alexandrasalazarz-lgtm/FunBioG14./ENTREGABLES/Taller 8/tati-quispe-cueva-bf5b25a1-1941-4490-aaff-6f8eaddafe3f-certificate.pdf

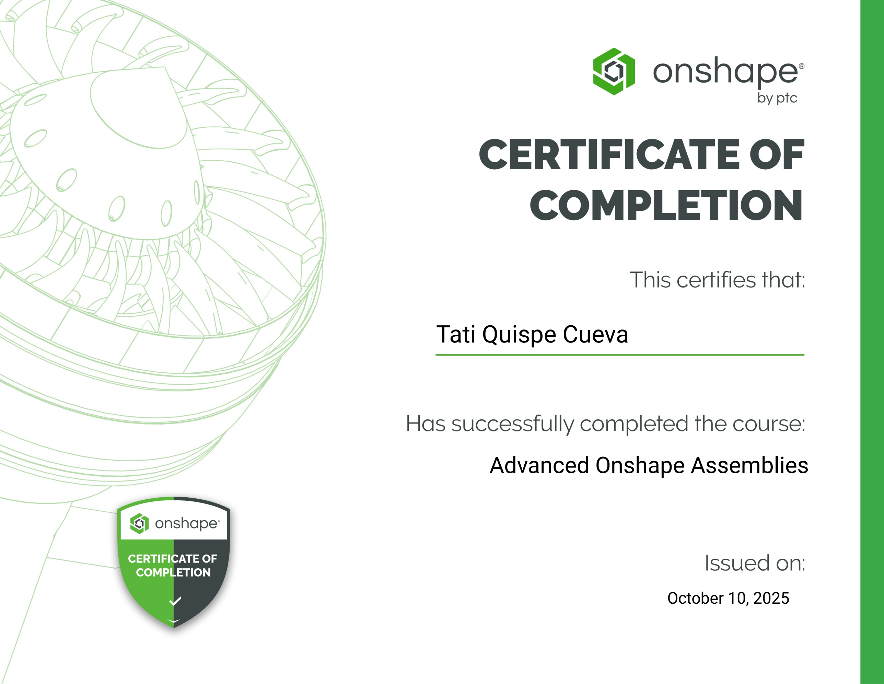
[picture p25: page 1]

Tati Quispe Cueva

Advanced Onshape Assemblies

October 10, 2025
