alexandrasalazarz-lgtm/FunBioG14./ENTREGABLES/Taller 8/sebastian-reymundo-b19e6a7e-2497-46d5-aa7a-b30fd2726343-certificate.pdf

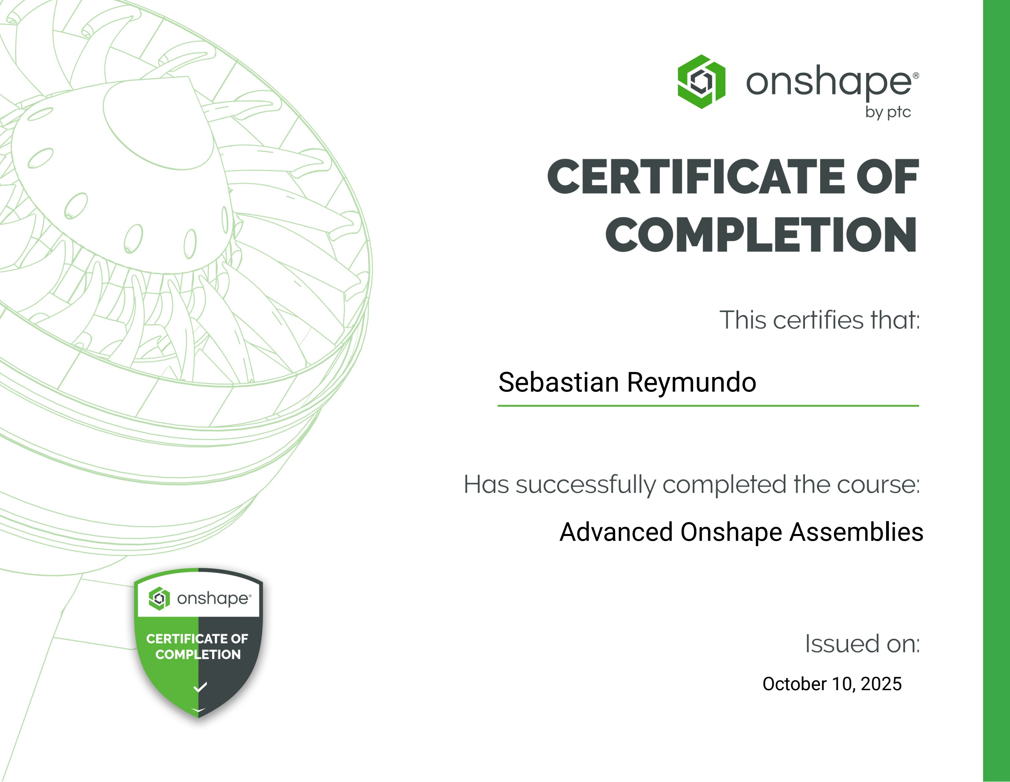
[picture p26: page 1]

Sebastian Reymundo

Advanced Onshape Assemblies

October 10, 2025
