alexandrasalazarz-lgtm/FunBioG14./ENTREGABLES/Taller 8/Luciana-Saenz-e1a2f70c-e385-4446-b01d-66b528b82a3a-certificate.PDF

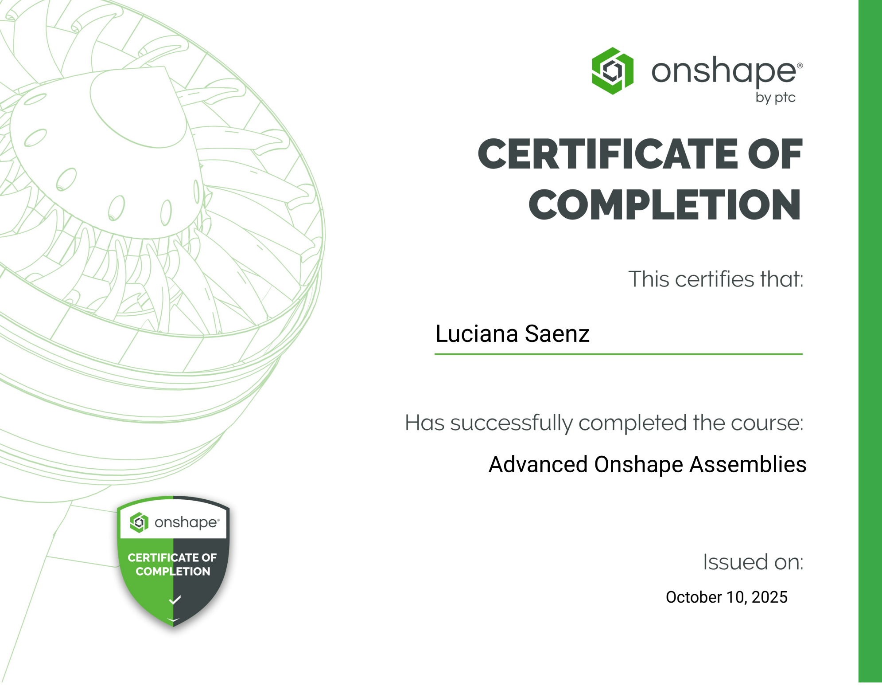
[picture p27: page 1]

Luciana Saenz

Advanced Onshape Assemblies

October 10, 2025
