alexandrasalazarz-lgtm/FunBioG14./ENTREGABLES/Taller 8/alexandra-salazar-3b08da2b-9840-4f47-ac77-2912e088a5ac-certificate.pdf

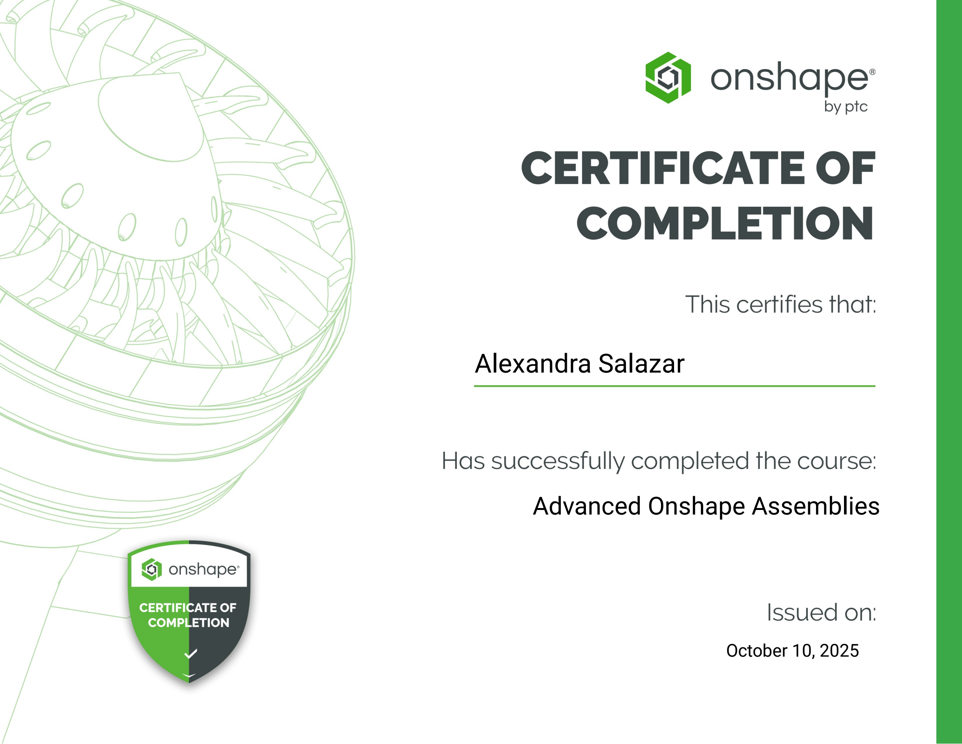
[picture p28: page 1]

Alexandra Salazar

Advanced Onshape Assemblies

October 10, 2025
