alexandrasalazarz-lgtm/FunBioG14./ENTREGABLES/Entregable 5/Sebastian Reymundo/Onshape Fundamentals CAD.pdf

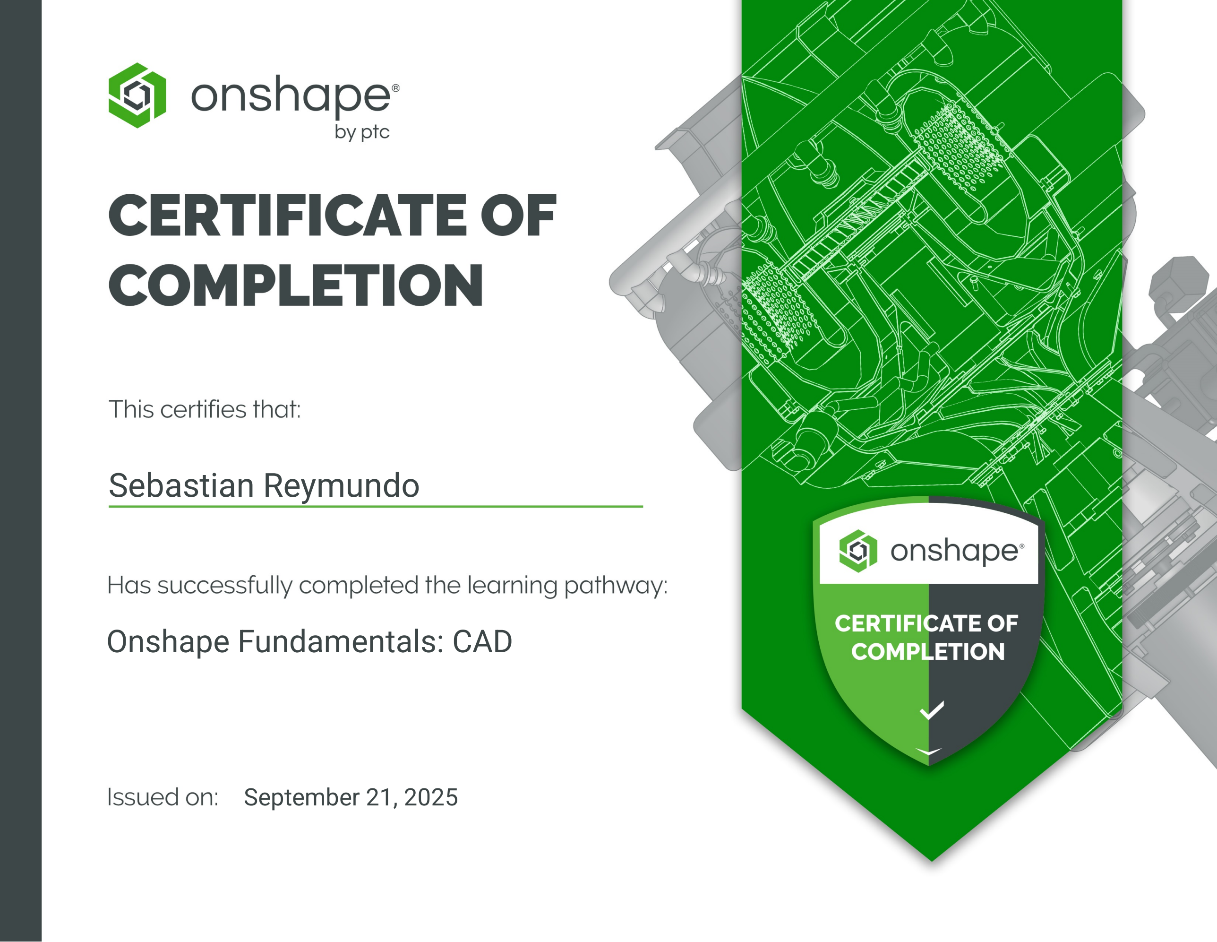
[picture p29: page 1]

Onshape Fundamentals: CAD

September 21, 2025

Sebastian Reymundo
