alexandrasalazarz-lgtm/FunBioG14./ENTREGABLES/Entregable 5/Luciana Saenz/luciana-saenz-2468588a-6642-499a-9439-9e74ae3b6bcc-certificate.pdf

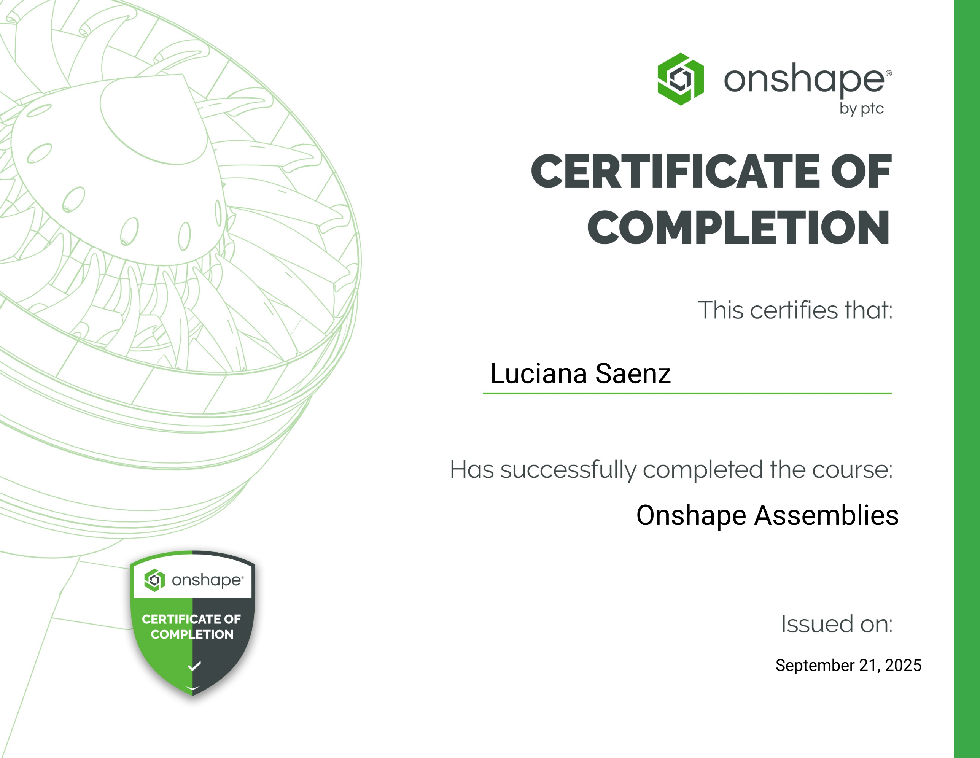
[picture p30: page 1]

Luciana Saenz

September 21, 2025

Onshape Assemblies
