alexandrasalazarz-lgtm/FunBioG14./ENTREGABLES/Entregable 5/Tatiana Quispe/tati-quispe-cueva-7f686d76-14ea-4a70-ba4c-fde4c63a0db2-certificate.pdf

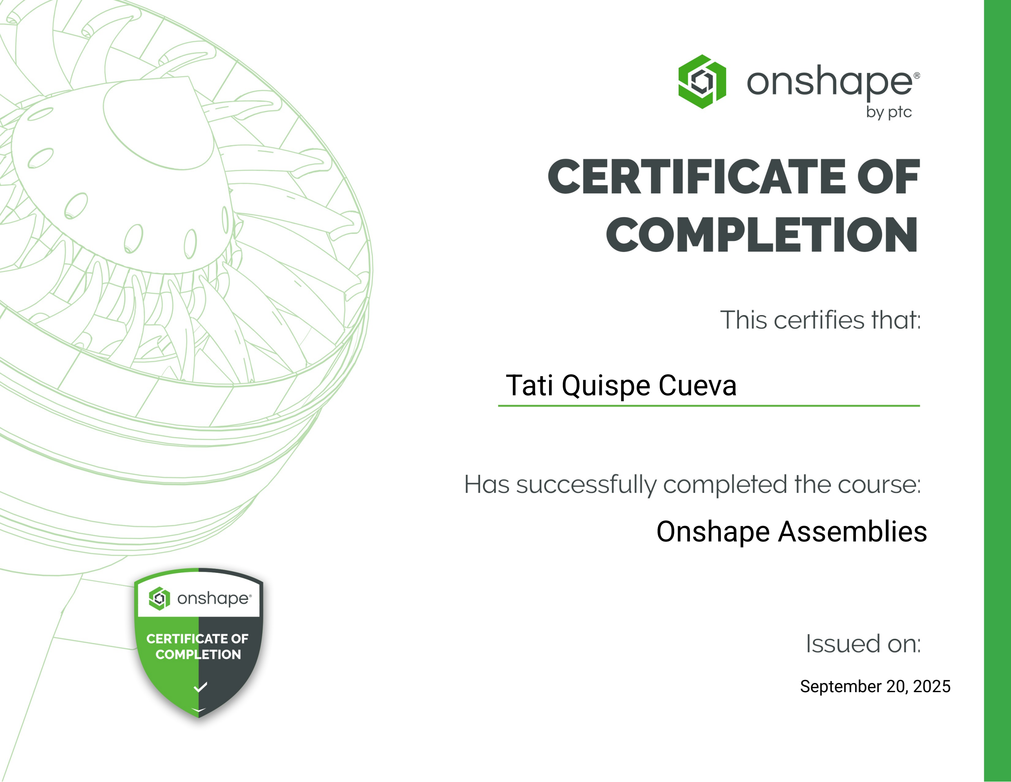
[picture p31: page 1]

Tati Quispe Cueva

September 20, 2025

Onshape Assemblies
