alexandrasalazarz-lgtm/FunBioG14./ENTREGABLES/Entregable 5/Alexandra Salazar/alexandra-salazar-a3af0b42-a987-454b-bc5e-5e8b458e8664-certificate.pdf

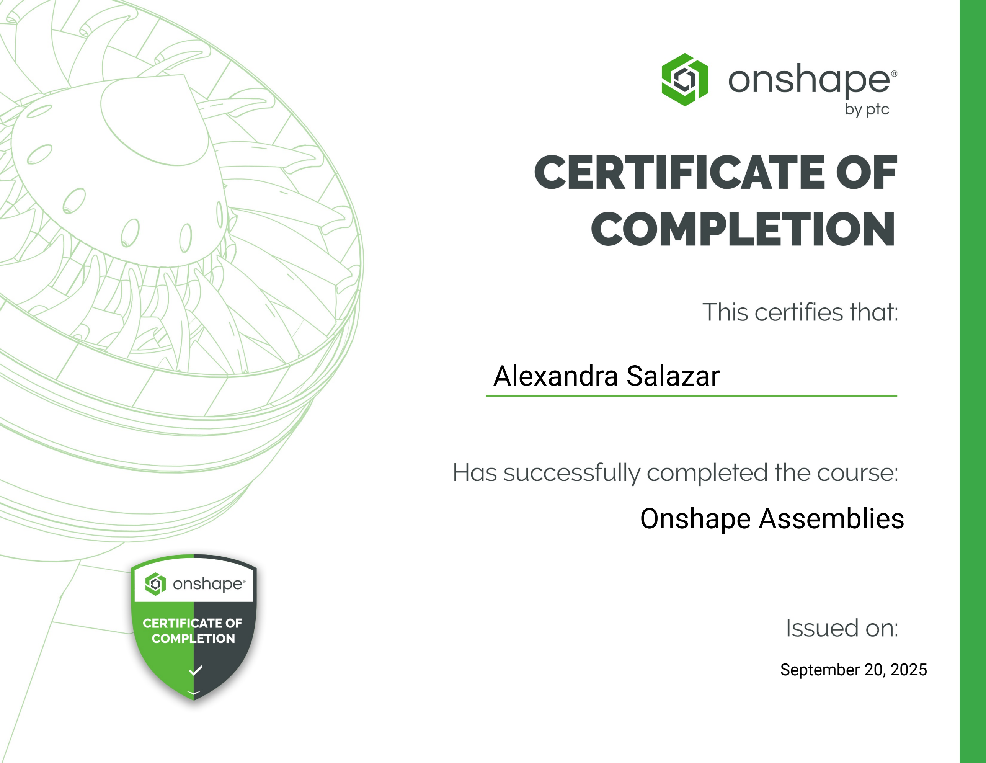
[picture p32: page 1]

Alexandra Salazar

September 20, 2025

Onshape Assemblies
