alexandrasalazarz-lgtm/FunBioG14./ENTREGABLES/Entregable 5/Alexandra Salazar/alexandra-salazar-1867dc95-b322-4a8a-b071-154235bd6980-certificate (1).pdf

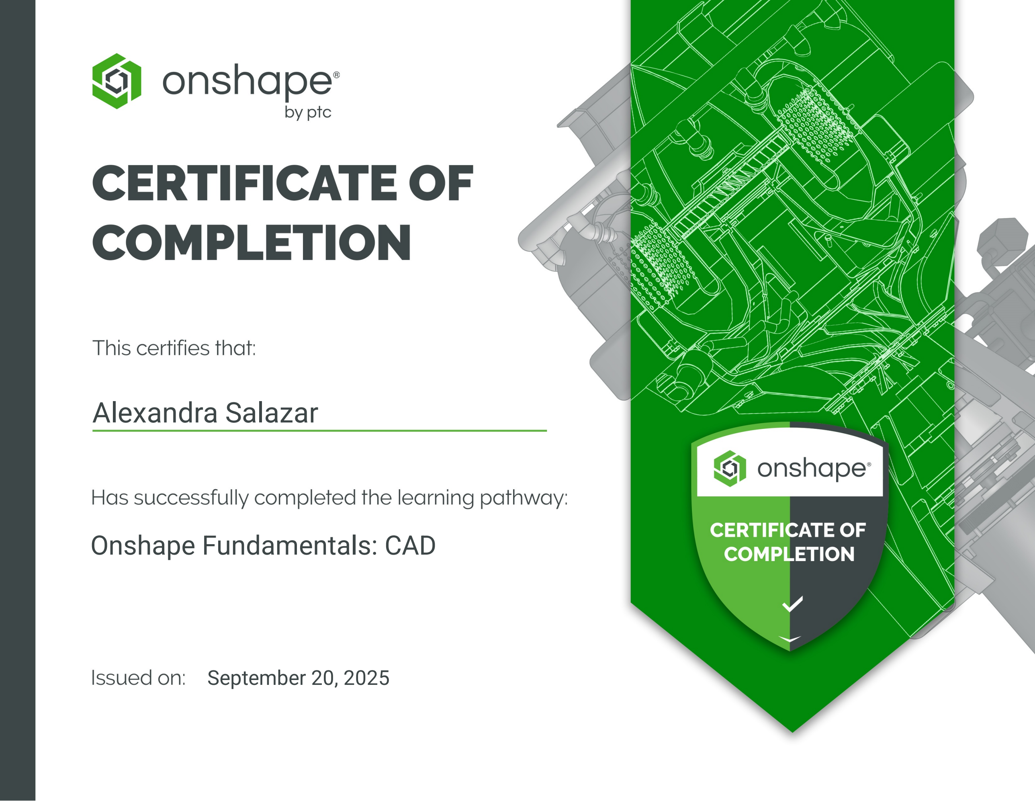
[picture p33: page 1]

Onshape Fundamentals: CAD

September 20, 2025

Alexandra Salazar
