alexandrasalazarz-lgtm/FunBioG14./DOCUMENTOS/HITO 2/HITO 2 presentación.pdf

## Fundamentos de Biodiseño

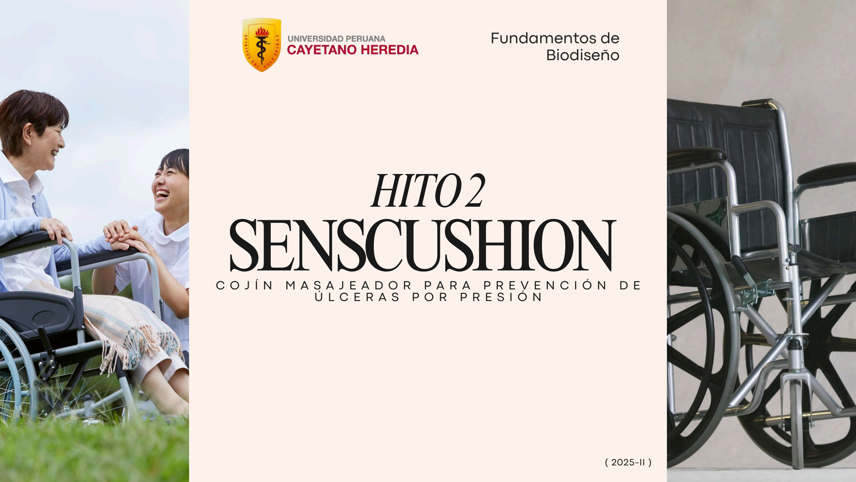
[picture p95: page 1]

# SENSCUSHION

( 2025-II )

# HITO2

C O J Í N | M A S A J E A D O R | P A R A | P R E V E N C I Ó N | D E
Ú L C E R A S | P O R | P R E S I Ó N

# INTEGRANTES: Rodríguez Cruz, Ivanna Jael (Investigación, Diseñadora y Programadora

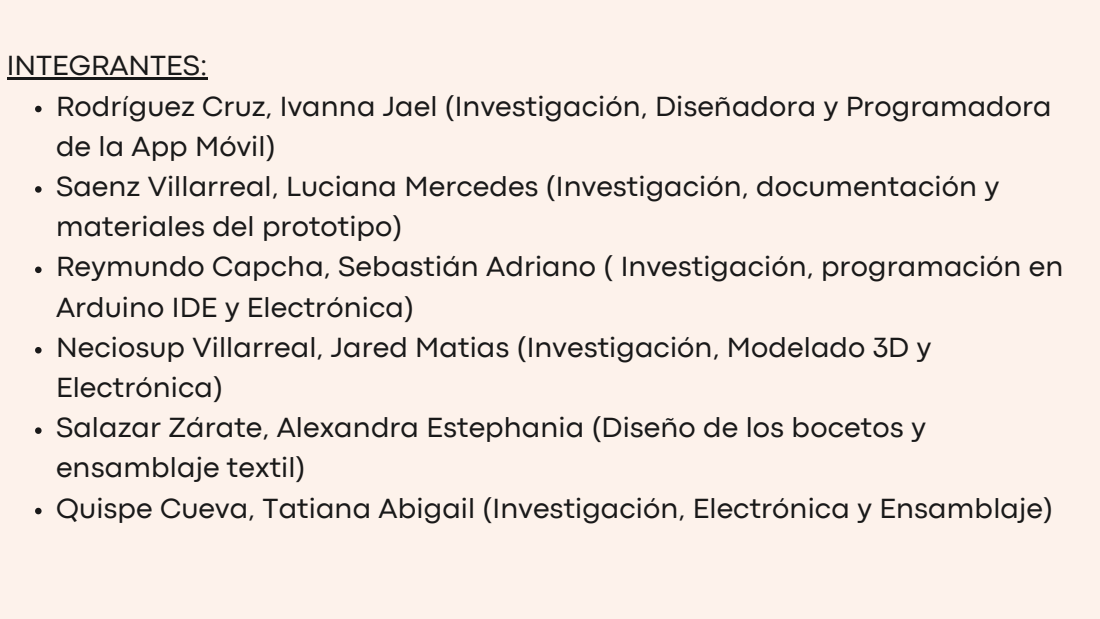
[picture p96: page 2]

de la App Móvil)
Saenz Villarreal, Luciana Mercedes (Investigación, documentación y
materiales del prototipo)
Reymundo Capcha, Sebastián Adriano ( Investigación, programación en
Arduino IDE y Electrónica)
Neciosup Villarreal, Jared Matias (Investigación, Modelado 3D y
Electrónica)
Salazar Zárate, Alexandra Estephania (Diseño de los bocetos y
ensamblaje textil)
Quispe Cueva, Tatiana Abigail (Investigación, Electrónica y Ensamblaje)

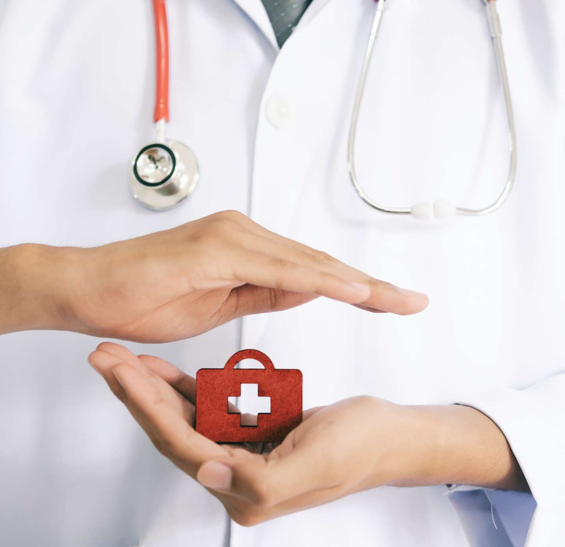
[picture p97: figure]

Í
N

D

I

C

E

( 0 7 )

0

1

## HIT

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
DIGIT
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
LIMIT

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
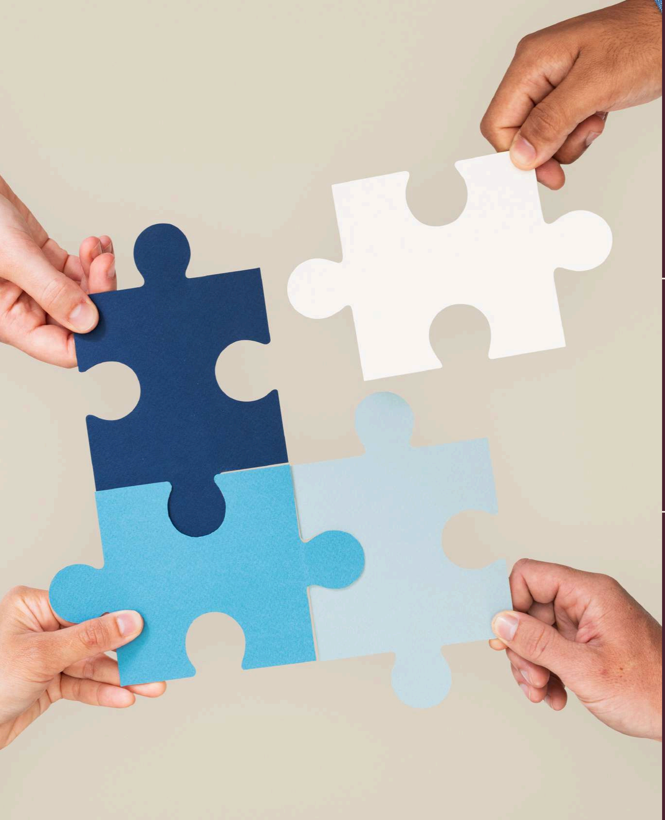
[picture p98: figure]

# PROBLEMÁTICA

## HITO 2

## FUNDAMENTOS DE BIODISEÑO

01

# Úlcerasporpresión

Se desarrolla cuando se bloquea el suministro de sangre a un área del cuerpo porque hay una presión excesiva y prolongada sobre la misma. En consecuencia, la piel en esa área comienza a morir, lo que resulta en una área abierta como un cráter o úlcera en la piel. [1]

FUNDAMENTOS DE BIODISEÑO | HITO 2 | ( 2025-II )

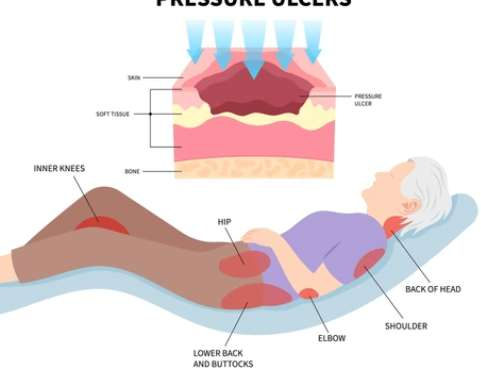
[picture p99: figure]

# Estadísticas

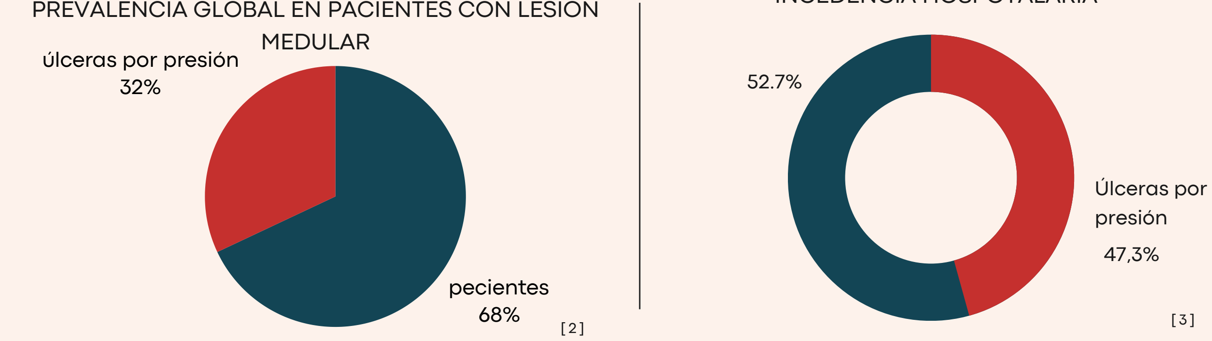
[picture p100: figure]
pecientes 68%; úlceras por presión 32%; Úlceras por; presión; MEDULAR

## PREVALENCIA GLOBAL EN PACIENTES CON LESIÓN

## INCEDENCIA HOSPOTALARIA

# Factoresderiesgo

FUNDAMENTOS DE BIODISEÑO | HITO 2 | ( 2025-II )

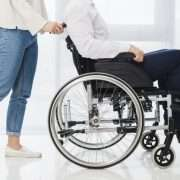
[picture p101: figure]

INMOVILIDAD
PROLONGADA

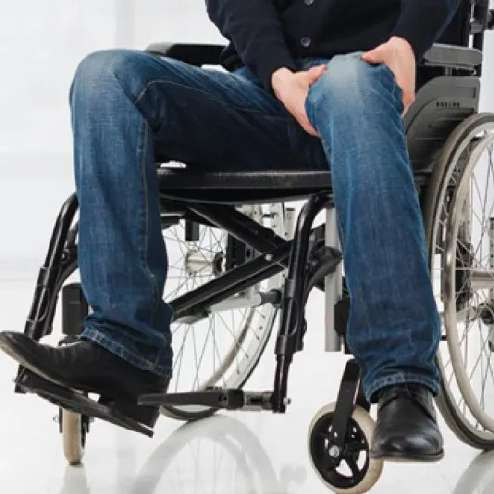
[picture p102: figure]

PÉRDIDA DE
SENSIBILIDAD

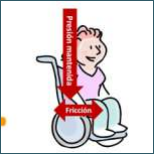
[picture p103: figure]
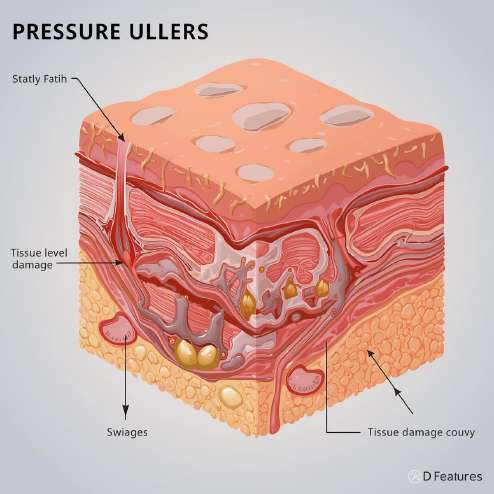
[picture p104: figure]
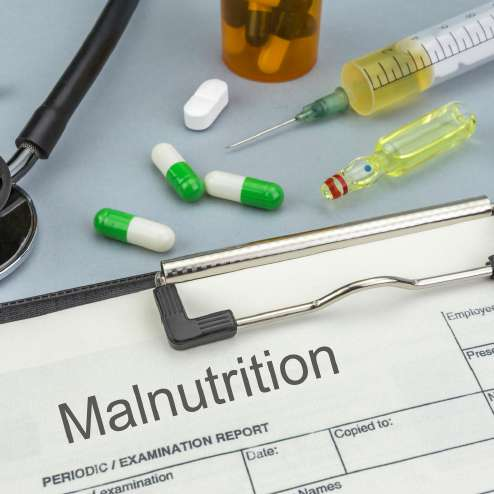
[picture p105: figure]

FRICCIÓN | HUMEDAD | MALNUTRICIÓN

# Cargaeconómica:

## Tratamiento de úlceras por presión genera

## costes directos significativos para el paciente [5]

[4]

# NECESIDADIDENTIFICADA

FUNDAMENTOS DE BIODISEÑO | ( PORTFOLIO DE TRABAJOS ) | 2025-II

# “Faltade un sistemaefectivoy accesibleparalaprevención de úlcerasporpresión

”

# Estadodelarte

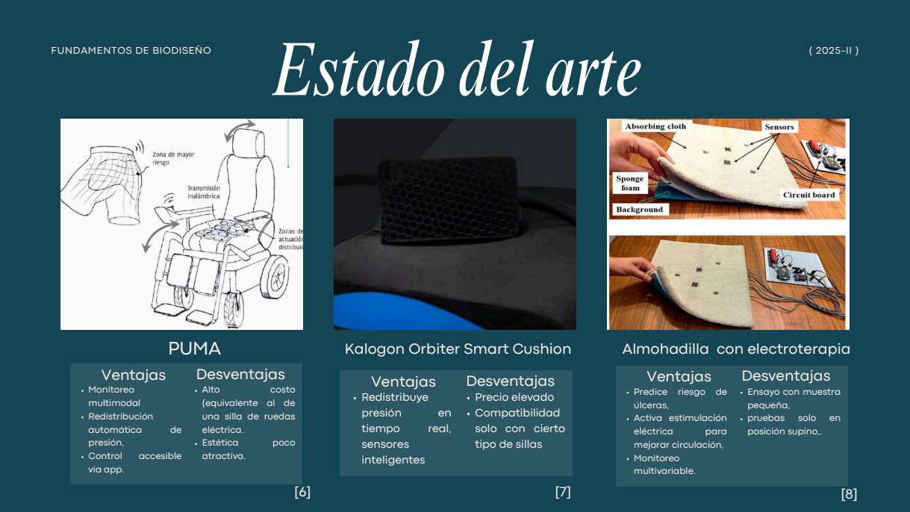
[picture p106: page 8]
PUMA; FUNDAMENTOS DE BIODISEÑO; Kalogon Orbiter Smart Cushion; Almohadilla con electroterapia; Ventajas; Desventajas; Monitoreo; multimodal; Redistribución; automática; presión,; Control; accesible; vía app.; Alto; costo; Estética; poco; Redistribuye; presión; tiempo; real,; sensores; inteligentes; Predice; riesgo; úlceras,; Activa estimulación; eléctrica; para; mejorar circulación,; multivariable.; pruebas; solo

(equivalente al de
una silla de ruedas
eléctrica.
atractiva.

Ensayo con muestra
pequeña,
posición supino,.

Precio elevado
Compatibilidad
solo con cierto
tipo de sillas

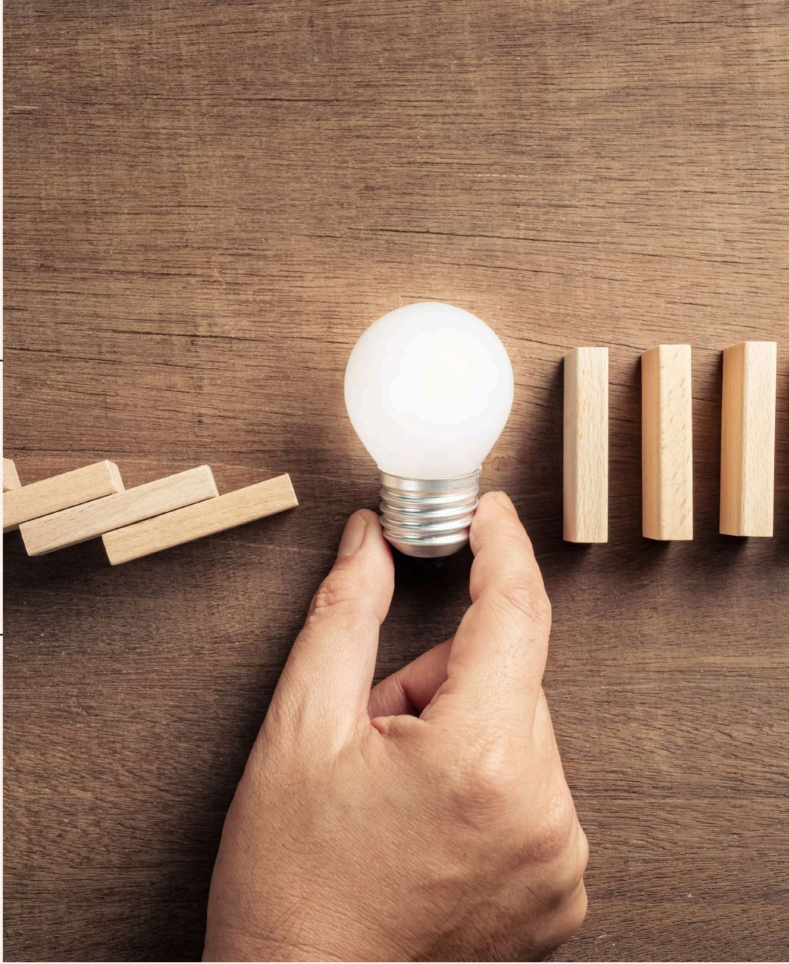
[picture p107: figure]

# SOLUCIÓN

## HITO 2

## FUNDAMENTOS DE BIODISEÑO

02

# SOLUCIÓN

FUNDAMENTOS DE BIODISEÑO | HITO 2

# “Cojín preventivo de úlceras por presión con

# masaje vibracionales”

# FUNCIONAMIENTO

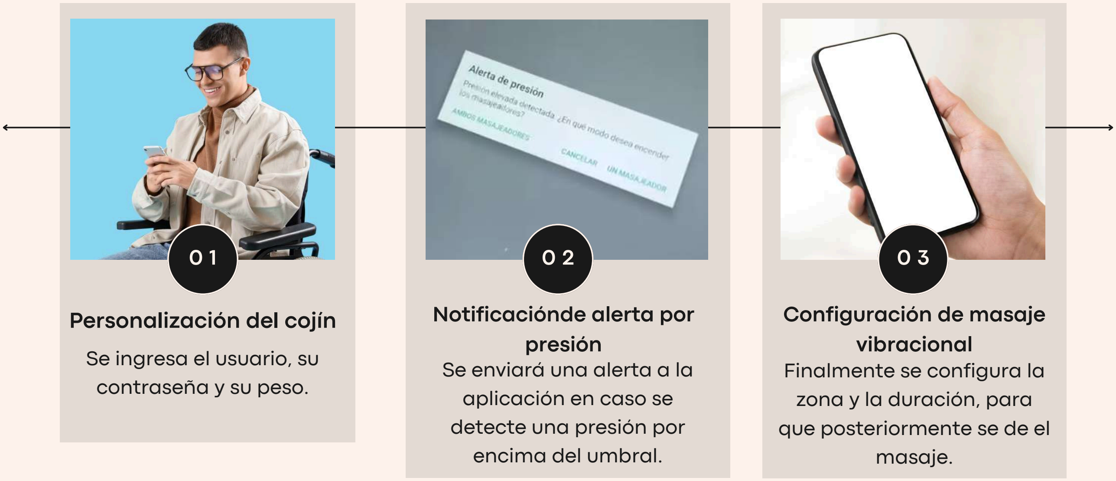
[picture p108: figure]
Se ingresa el usuario, su; contraseña y su peso.; Personalización del cojín; Se enviará una alerta a la; aplicación en caso se; detecte una presión por; encima del umbral.; Notificaciónde alerta por; presión; Finalmente se configura la; zona y la duración, para; que posteriormente se de el; masaje.; Configuración de masaje; vibracional

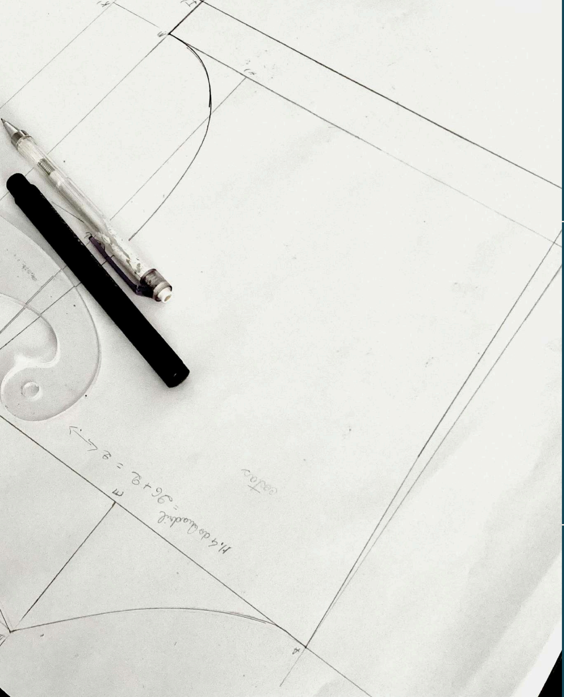
[picture p109: figure]

# BOCETO Y MODELADO

## HITO 2

## FUNDAMENTOS DE BIODISEÑO

03

# Bocetoymodelado

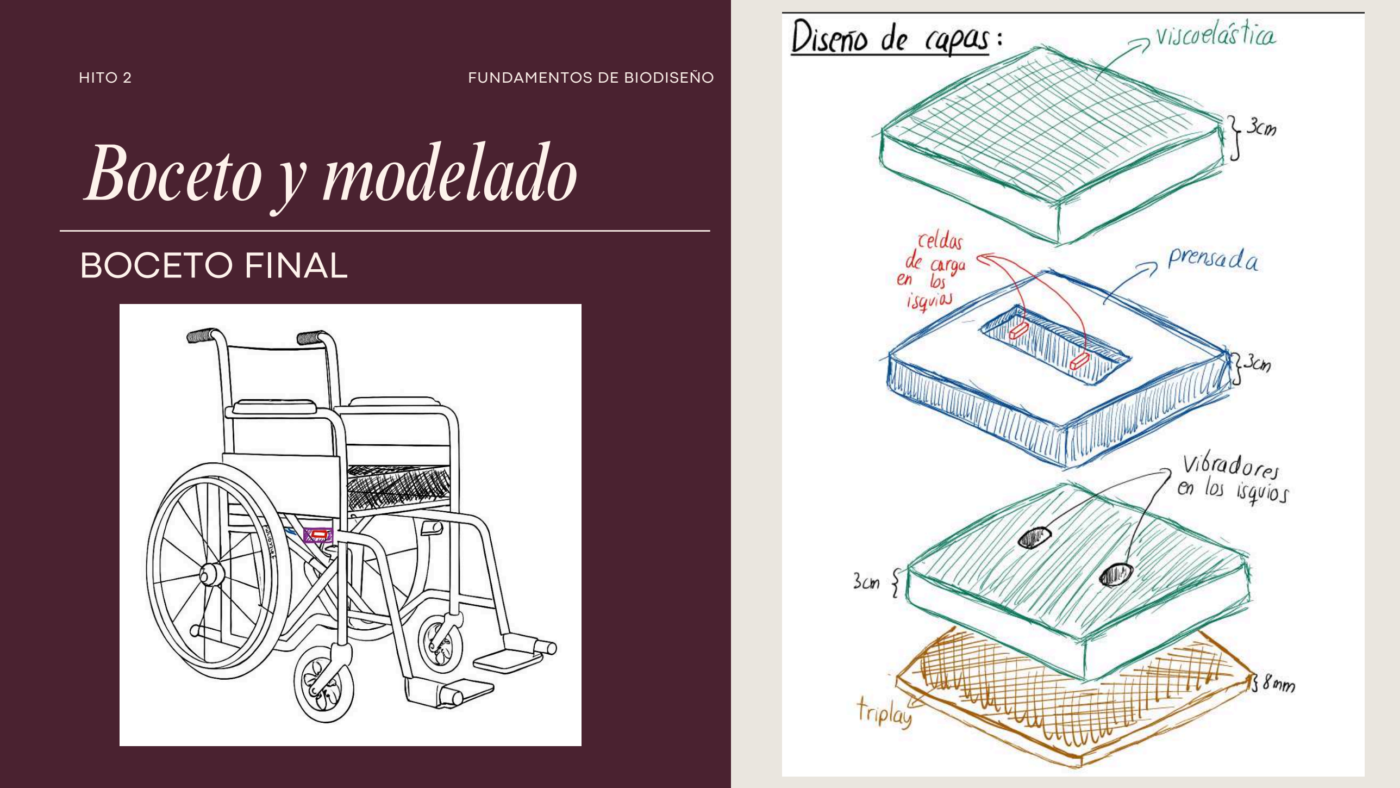
[picture p110: page 12]

HITO 2 | FUNDAMENTOS DE BIODISEÑO

# BOCETO FINAL

HITO 2 | FUNDAMENTOS DE BIODISEÑO | HITO 2

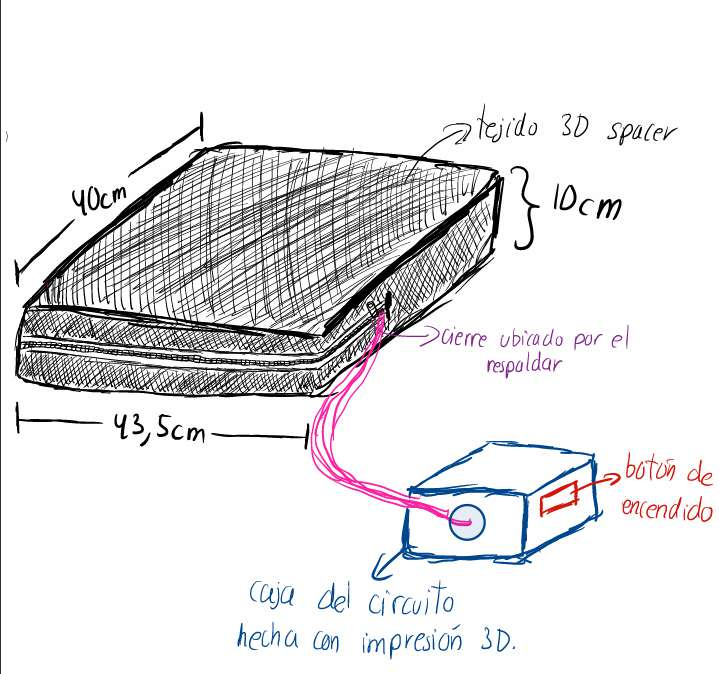
[picture p111: figure]

# MODELADO3D

HITO 2 | FUNDAMENTOS DE BIODISEÑO | HITO 2

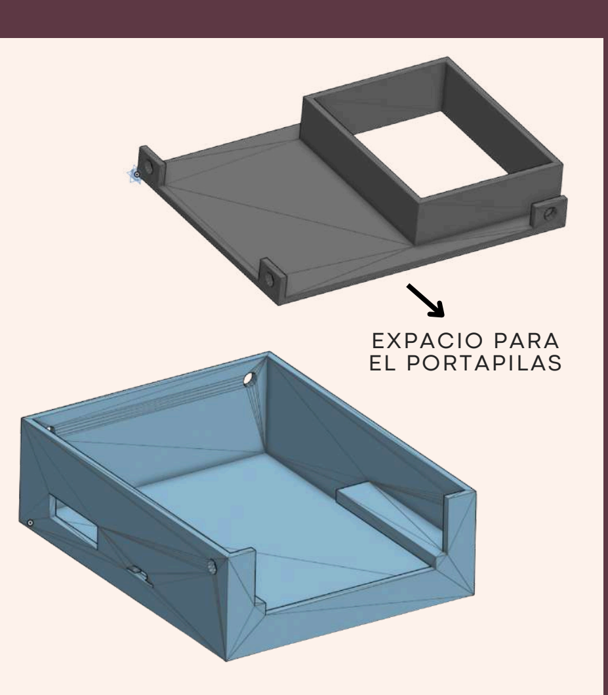
[picture p112: figure]
EXPACIO PARA EL PORTAPILAS
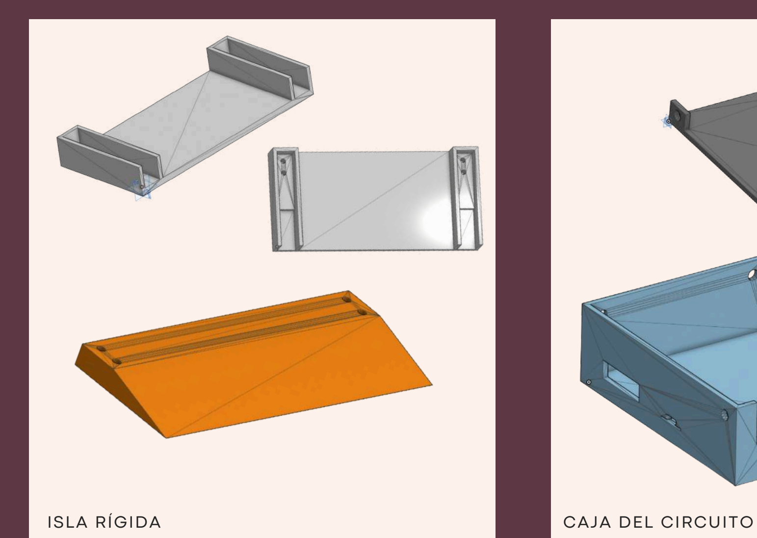
[picture p113: figure]
ISLA RÍGIDA; CAJA DEL CIRCUITO

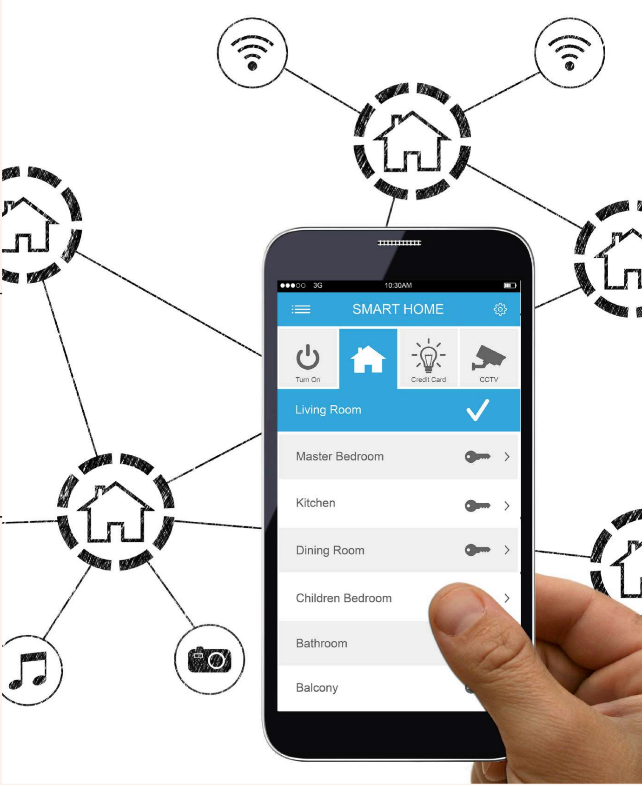
[picture p114: figure]

# APLICATIVO

## HITO 2

## FUNDAMENTOS DE BIODISEÑO

04

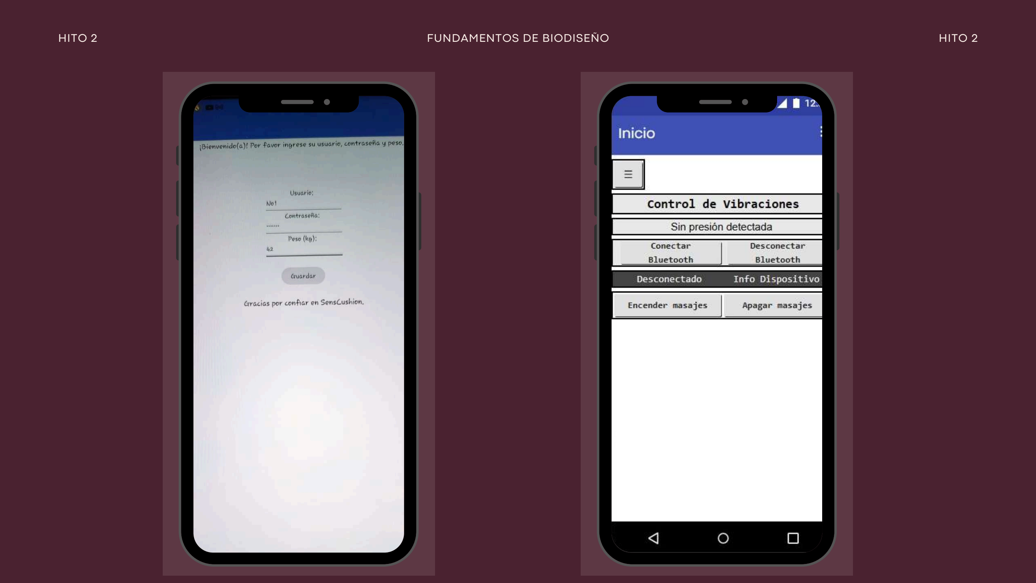
[picture p115: page 16]

HITO 2 | FUNDAMENTOS DE BIODISEÑO | HITO 2

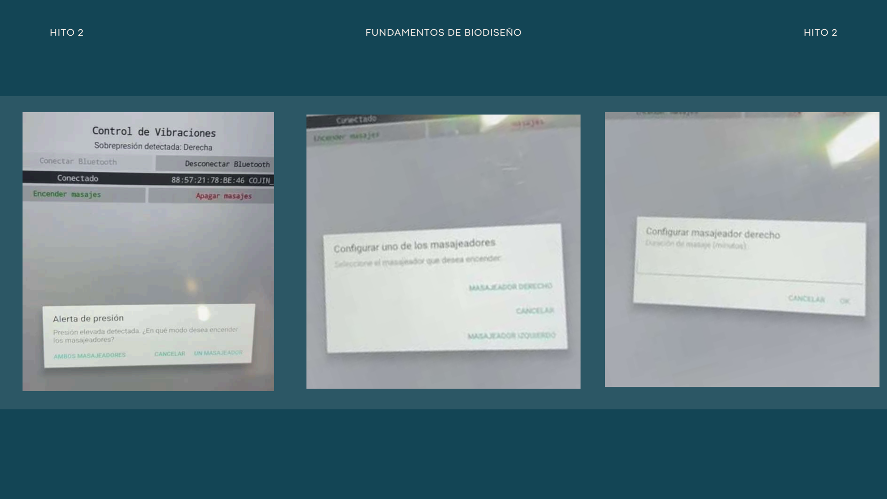
[picture p116: page 17]

HITO 2 | FUNDAMENTOS DE BIODISEÑO | HITO 2

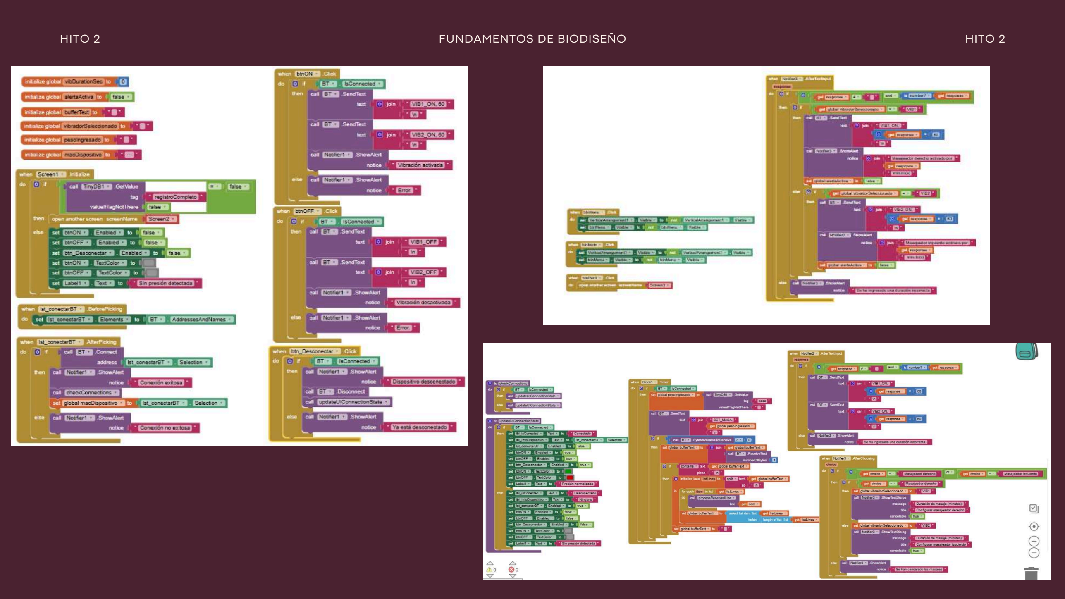
[picture p117: page 18]

HITO 2 | FUNDAMENTOS DE BIODISEÑO | HITO 2

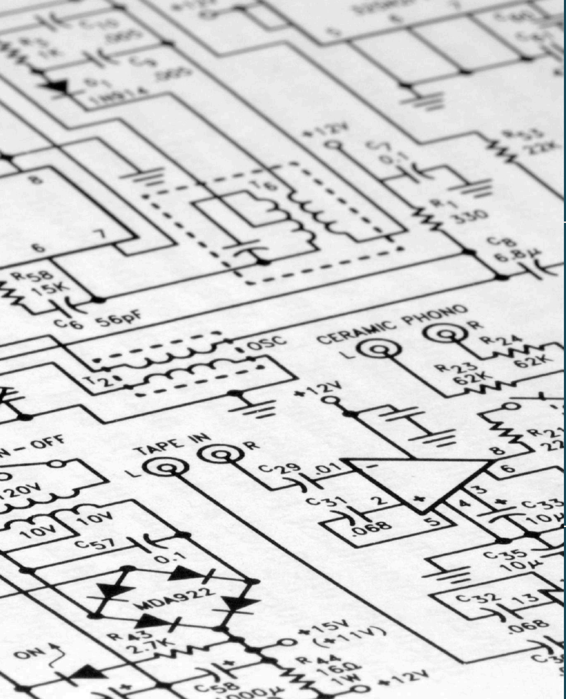
[picture p118: figure]

# DIAGRAMADEL PROTOTIPO

## HITO 2

## FUNDAMENTOS DE BIODISEÑO

05

# Diagramaesquemáticodelprototipoelectrónico

FUNDAMENTOS DE BIODISEÑO | HITO 2 | ( 2025-II )

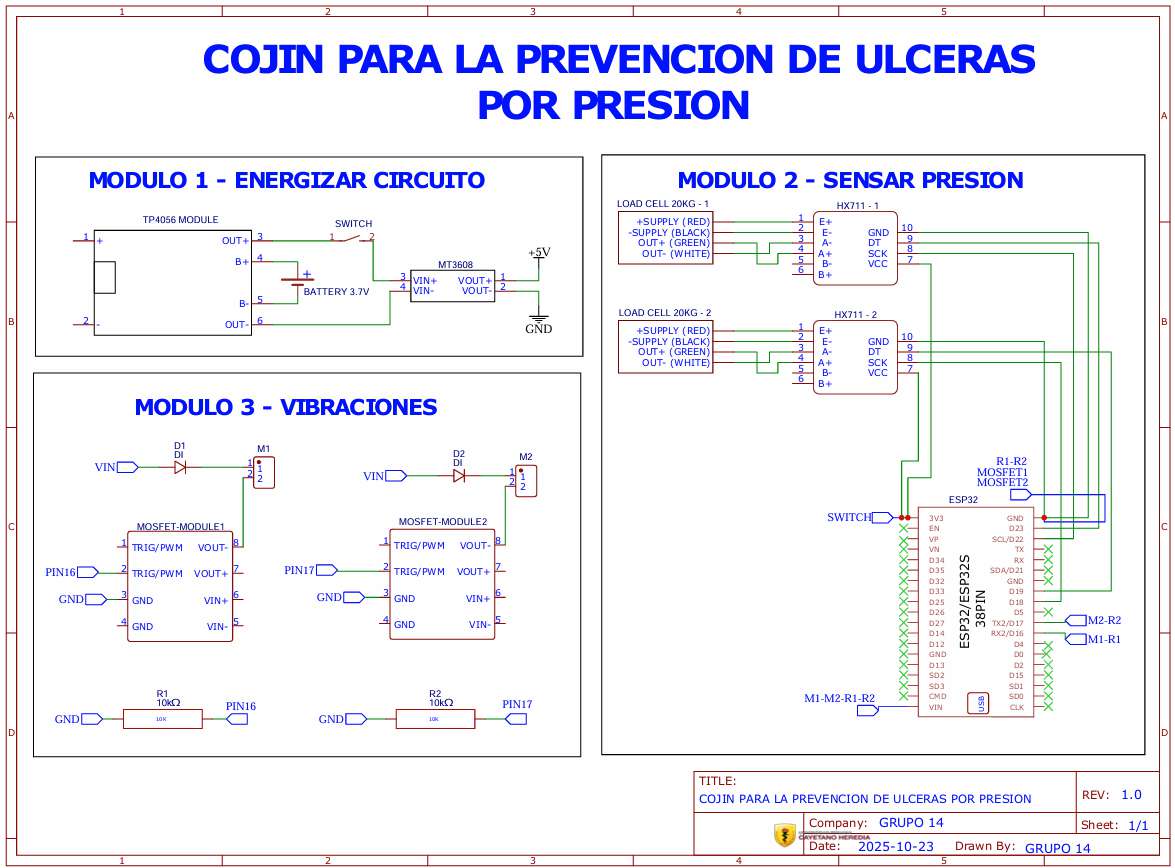
[picture p119: figure]

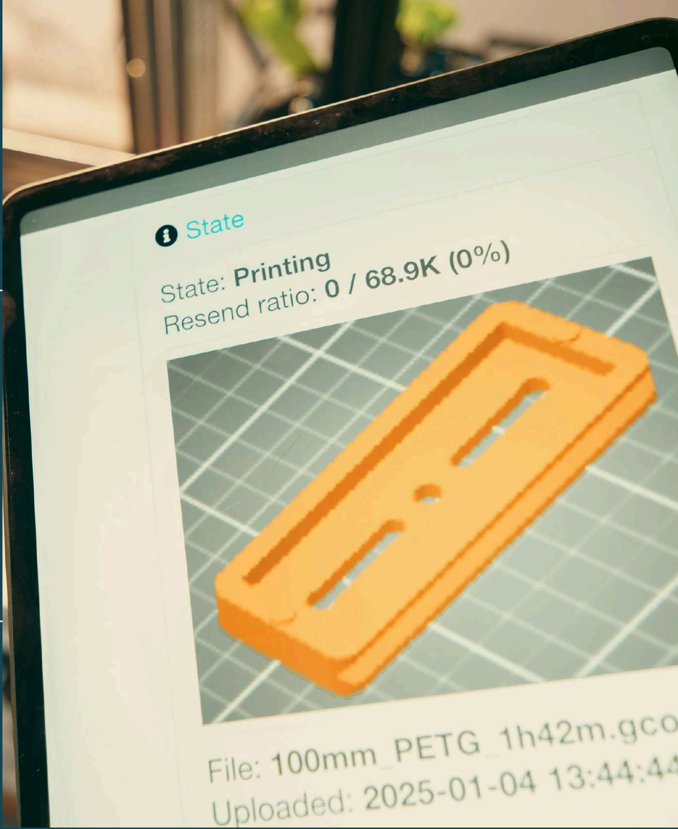
[picture p120: figure]

# MANUFACTURA DIGITAL

## HITO 2

## FUNDAMENTOS DE BIODISEÑO

06

# PROCESO DE ENSAMBLAJE

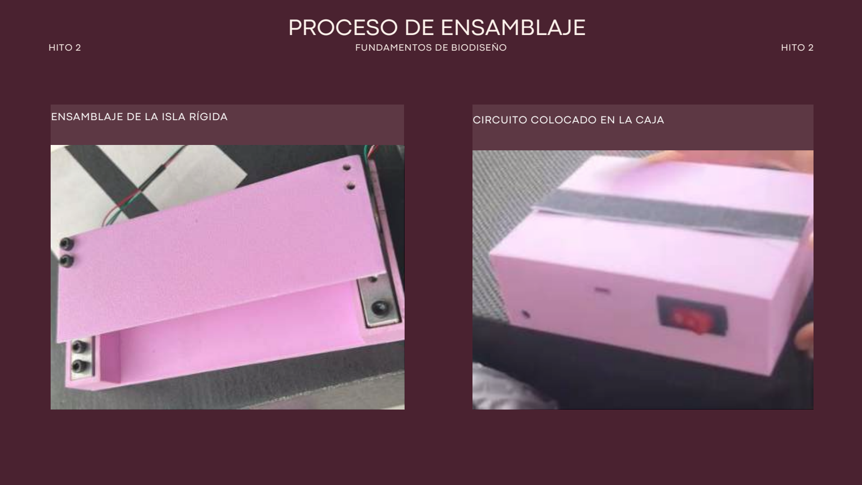
[picture p121: page 22]

ENSAMBLAJE DE LA ISLA RÍGIDA | CIRCUITO COLOCADO EN LA CAJA
HITO 2 | FUNDAMENTOS DE BIODISEÑO | HITO 2

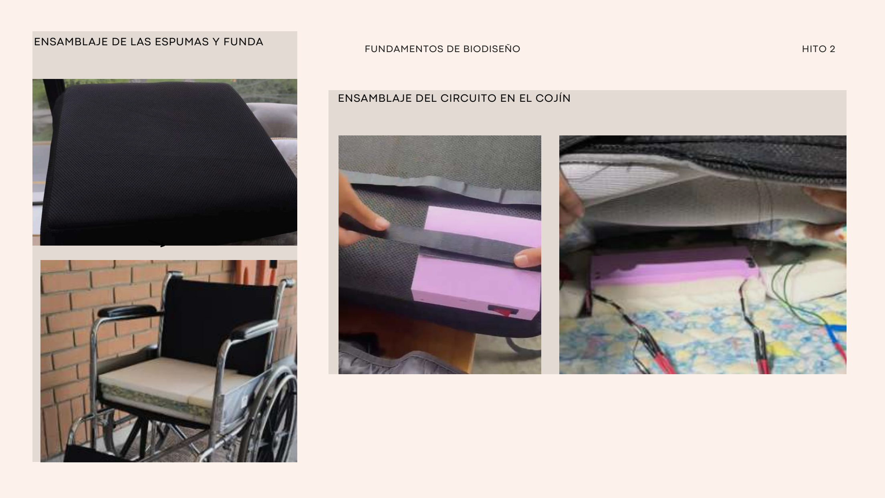
[picture p122: page 23]

ENSAMBLAJE DE LAS ESPUMAS Y FUNDA

ENSAMBLAJE DEL CIRCUITO EN EL COJÍN

FUNDAMENTOS DE BIODISEÑO | HITO 2

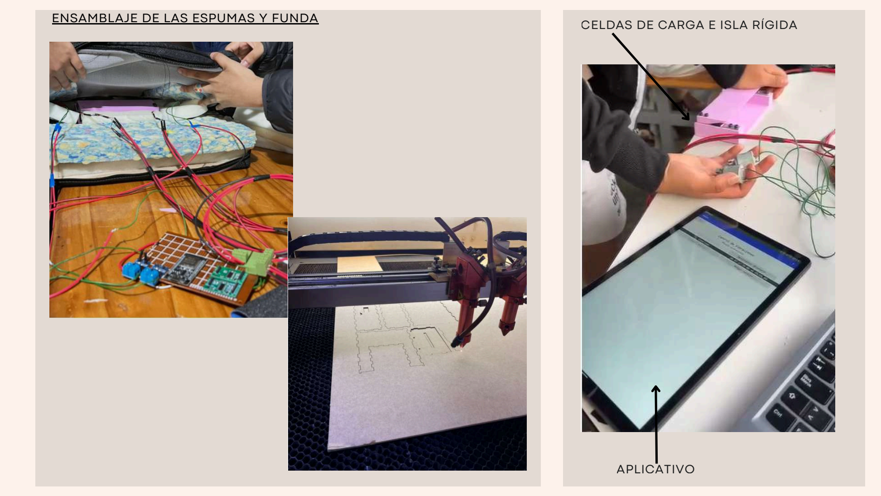
[picture p123: page 24]

CELDAS DE CARGA E ISLA RÍGIDA

APLICATIVO

ENSAMBLAJE DE LAS ESPUMAS Y FUNDA

Ga

# lle

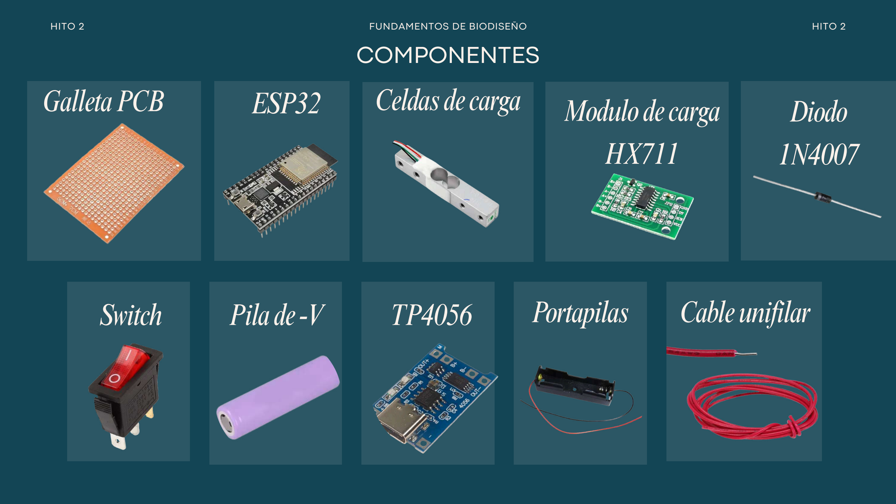
[picture p124: page 25]

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
# ifi

la
r

ta

P

CB

# ESP3

2

Ce

# lda

s

de
ca

# rga

Sw

# itch

Po

# rtap

i

la

# s COM

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
# rga

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
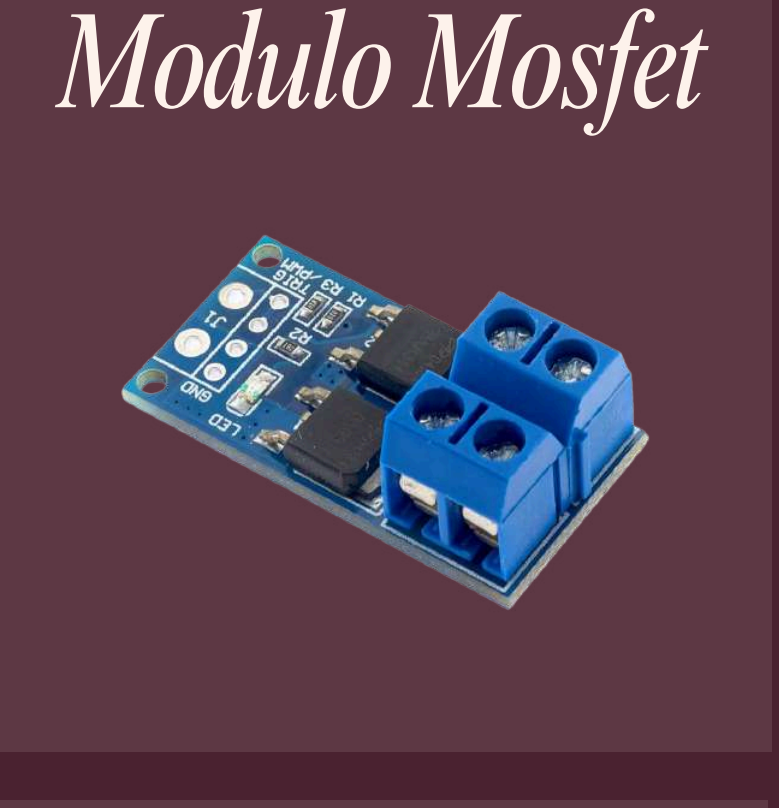
[picture p125: figure]
ModuloMosfet
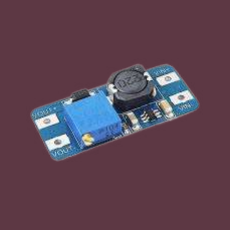
[picture p126: figure]
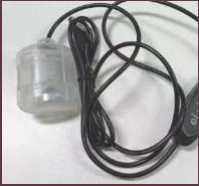
[picture p127: figure]

# Resistencias

# Convertidorde voltajeDCDC

# COMPONENTES

HITO 2 | FUNDAMENTOS DE BIODISEÑO | HITO 2

# Motoresde vibración

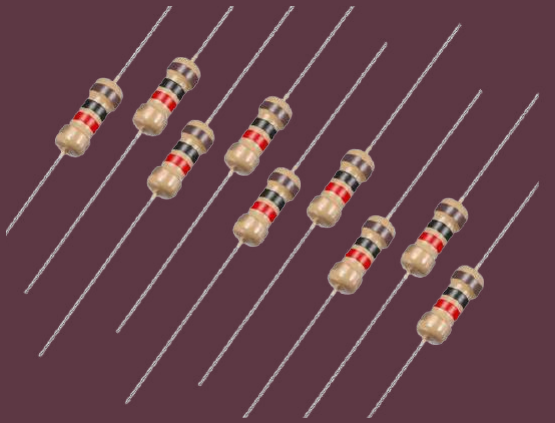
[picture p128: figure]

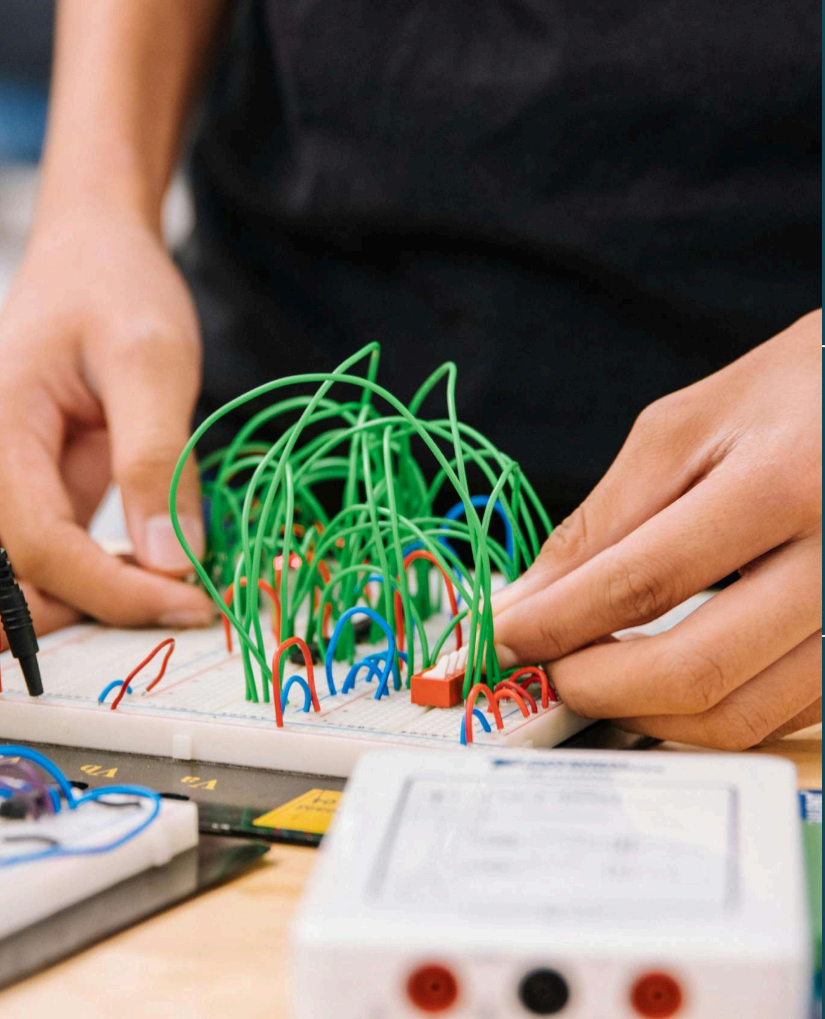
[picture p129: figure]

# PROTOTIPO

## HITO 2

## FUNDAMENTOS DE BIODISEÑO

07

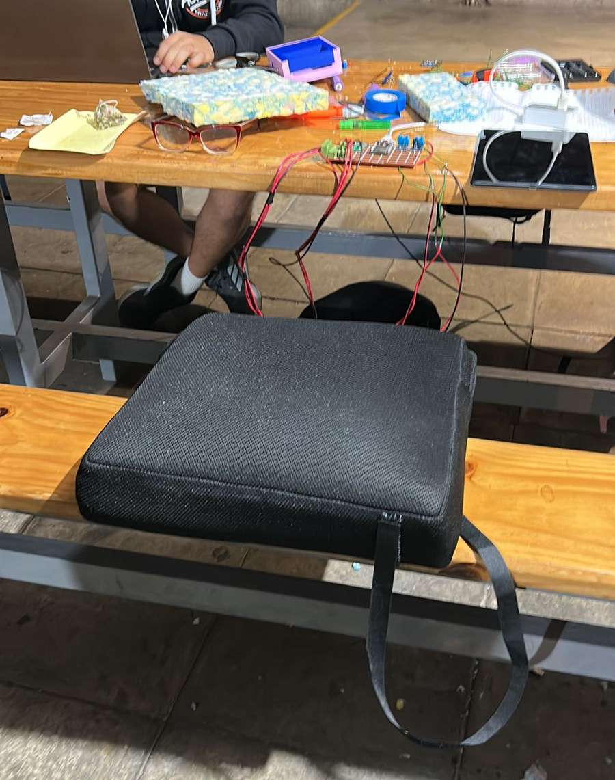
[picture p130: figure]

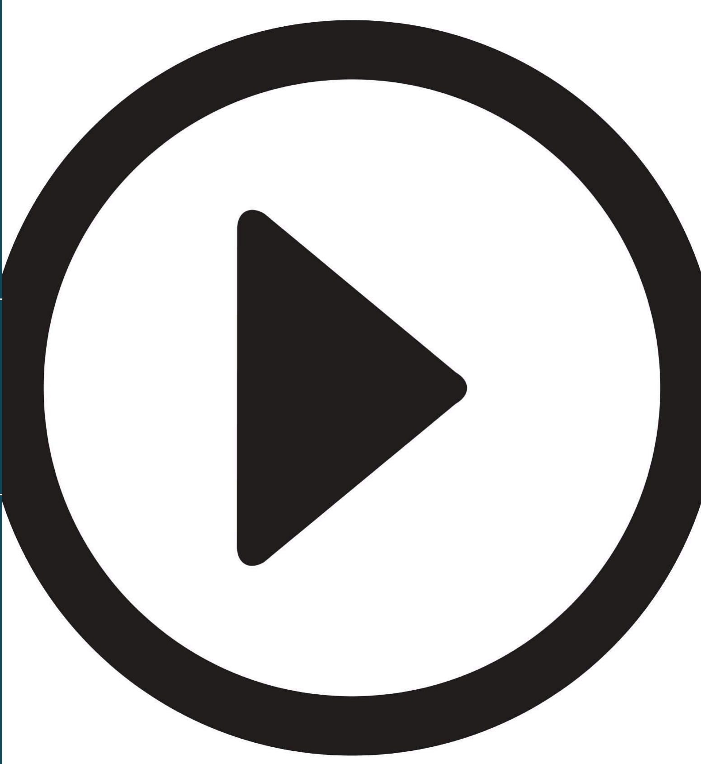
[picture p131: figure]

# DEMO

## HITO 2

## FUNDAMENTOS DE BIODISEÑO

07

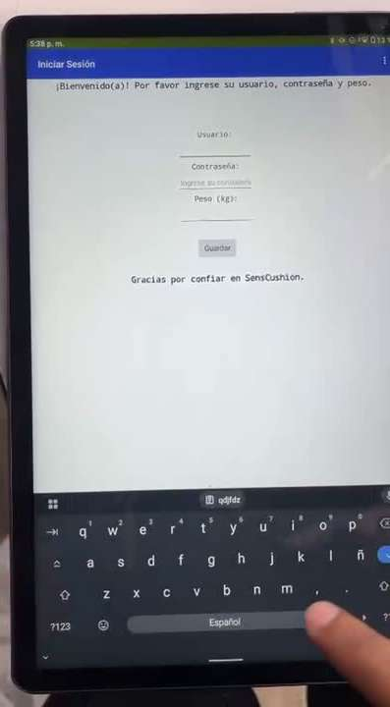
[picture p132: figure]

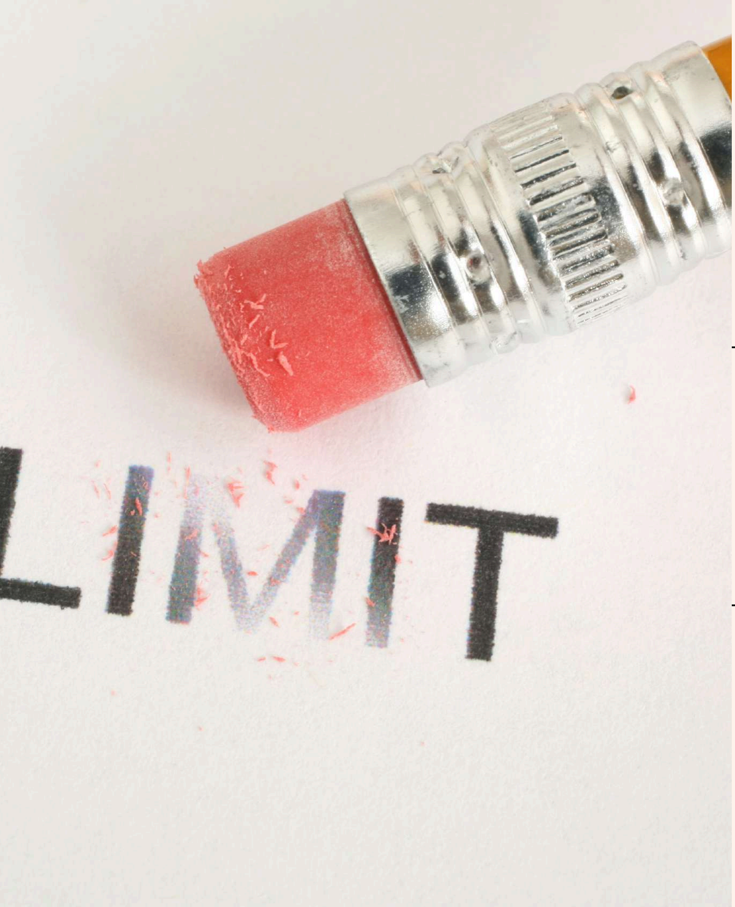
[picture p133: figure]

# LIMITACIONES

## HITO 2

## FUNDAMENTOS DE BIODISEÑO

09

La aplicación presenta fallos o funcionamiento limitado en dispositivos iOS, lo que reduce la accesibilidad del sistema a usuarios.

# LIMITACIONES

HITO 2 | FUNDAMENTOS DE BIODISEÑO | HITO 2

# Compatibilidad restringida

# Faltade monitoreo del nivelde batería

# Deformación de laespuma viscoelásticacon uso prolongado

La ausencia de un indicador de batería (alerta) impide al usuario saber cuándo debe recargar o reemplazar las baterías, lo que puede interrumpir el funcionamiento del dispositivo

Aumenta el riesgo de que el usuario ejerza presión directa sobre el circuito interno, con posible daño mecánico o eléctrico.

# Referencias

[1] American Cancer Society, "Úlceras por presión," American Cancer Society (español), Actualizado: 1-Feb-2020. [Online]. Available:

https://www.cancer.org/es/cancer/como-sobrellevar-el-cancer/efectos-secundarios/piel-cabello-unas/ulceras-por-presion.html [Accessed: 25-Nov-2025]

( BORIS CARVAJAL ) | ( PORTFOLIO DE TRABAJOS ) | ( 2035 )

[3]. Chen, Y. Wu, and Y. He, "Incidence of hospital-acquired pressure ulcers in acute spinal cord injury: a retrospective cohort study," Spinal Cord, vol. 55, no. 11, pp. 1046–1052, Nov. 2017. doi: 10.1038/sc.2017.67. [Online]. Available: https://www.nature.com/articles/sc201767 {Accesed: 25 nov 2025]

[2] W. S. Shiferaw, T. Y. Akalu, H. Mulugeta, and Y. A. Aynalem, "The global burden of pressure ulcers among patients with spinal cord injury: a systematic review and meta-analysis," BMC Musculoskeletal Disorders, vol. 21, no. 334, pp. 1–10, May 2020. doi: 10.1186/s12891-020-03369-0. [Online]. Available: https://link.springer.com/article/10.1186/s12891-020-03369-0 [Accessed: 25-Nov-2025]

[4]. [1] D. A. Aznar Sanz, L. Pinilla Varona, C. López Hernández, and B. Gadea Uribarri, “Factores de riesgo y prevención de las úlceras por presión,” Revista Sanitaria de Investigación, Oct. 21, 2021. [Online]. Available: https://revistasanitariadeinvestigacion.com/factores-de-riesgo-y-prevencion-de-las-ulceras-por-presion/

[5]. A. Gefen, “The biomechanics of sitting-acquired pressure ulcers in patients with spinal cord injury or lesions,” International Wound Journal, vol. 4, no. 3, pp. 222–231, Sep. 2007, doi: 10.1111/j.1742-481X.2007.00330.x

[6]J. L. Hernández, E. Ripoll, M. M. L. Vicente, J. F. G. Plà, F. F. Ros, R. B. Guillem, et al., "PUMA: Adiós a las úlceras por presión," Revista Biomecánica, pp. 86–96, 2015. [Online]. Available: https://share.google/bs2mNyDD5Uicakdc4 [Accessed: 25-Nov-2025] (https://www.nature.com/articles/sc201767)

[7] D. Coldewey, "Kalogon's smart cushion for wheelchairs keeps the pressure off and brings in $3.3M," TechCrunch, Sep. 2022. [Online]. Available: https://techcrunch.com/2022/09/22/kalogons-smart-cushion-for-wheelchairs-keeps-the- pressure-off-and-brings-in-3-3m {Accesed: 25 nov 2025]

[8][3] Z. S. Saleh, A. Q. Al-Neami, and H. K. Raad, "Smart Monitoring Pad for Prediction of Pressure Ulcers with an Automatically Activated Integrated Electro-Therapy System," Designs, vol. 5, no. 3, p. 47, 2021. doi: 10.3390/designs5030047. [Online]. Available: https://doi.org/10.3390/designs5030047 {Accesed: 25 nov 2025]

# MUCHAS GRACIAS

## FUNDAMENTOS DE BIODISEÑO

## HITO 2
