alexandrasalazarz-lgtm/FunBioG14./ENTREGABLES/Entregable 5/Sebastian Reymundo/Detailed Drawings.pdf

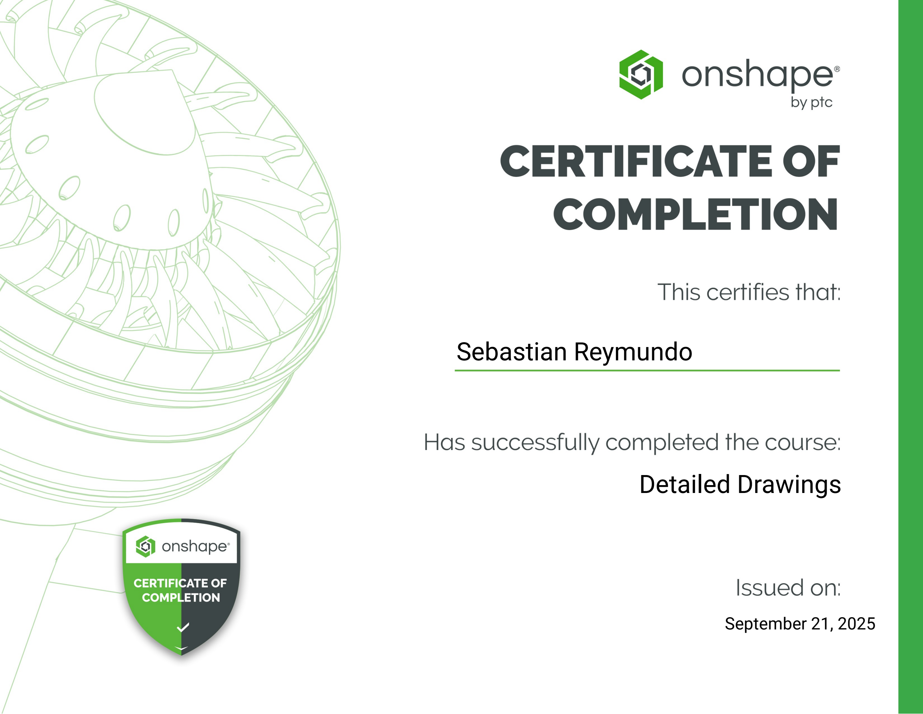
[picture p140: page 1]

Sebastian Reymundo

September 21, 2025

Detailed Drawings
