alexandrasalazarz-lgtm/FunBioG14./ENTREGABLES/Entregable 5/Sebastian Reymundo/Introduction to Part Studios.pdf

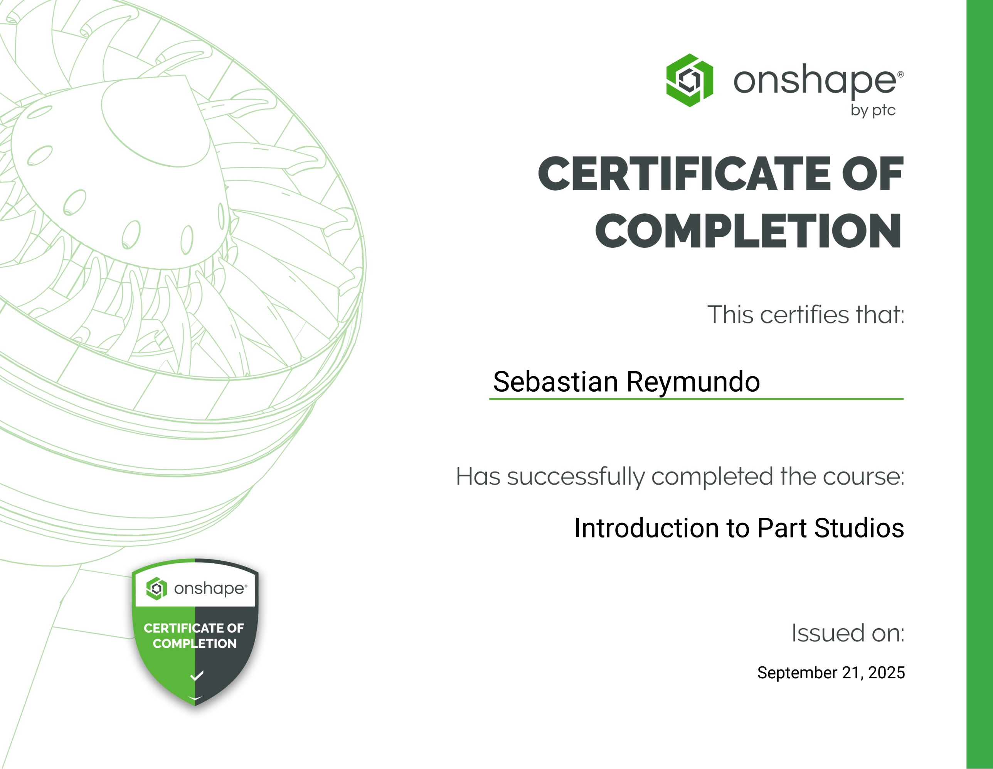
[picture p141: page 1]

Sebastian Reymundo

Introduction to Part Studios

September 21, 2025
