alexandrasalazarz-lgtm/FunBioG14./ENTREGABLES/Entregable 5/Sebastian Reymundo/Introduction to Sketching.pdf

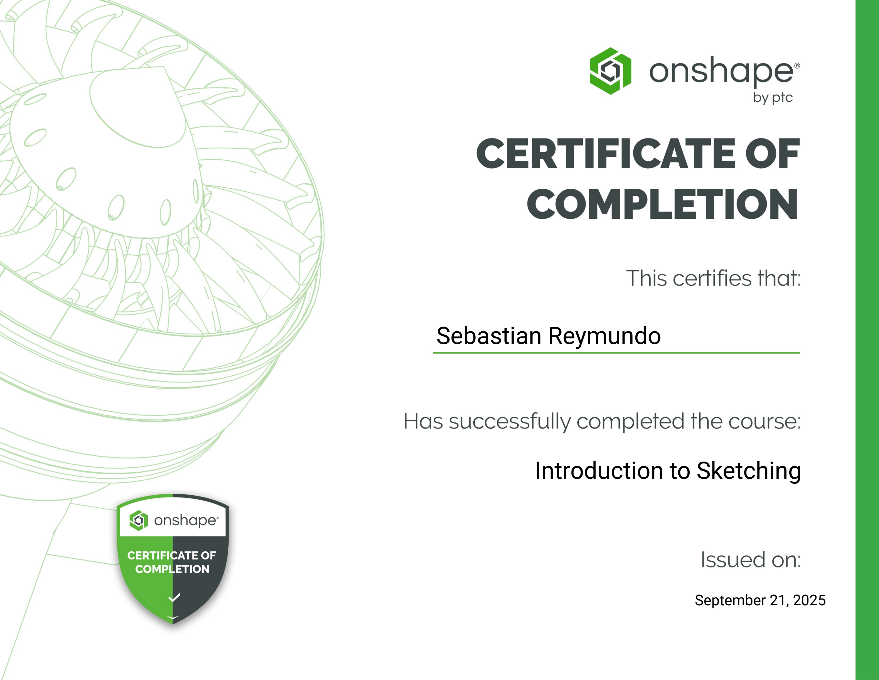
[picture p142: page 1]

Sebastian Reymundo

Introduction to Sketching

September 21, 2025
