alexandrasalazarz-lgtm/FunBioG14./ENTREGABLES/Entregable 5/Sebastian Reymundo/Multi-Part Part Studios.pdf

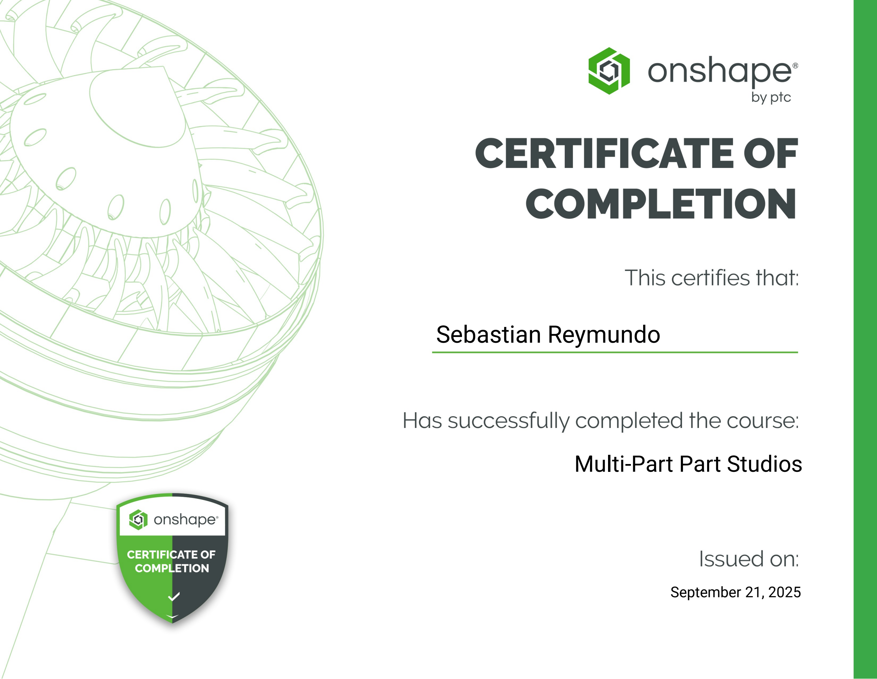
[picture p143: page 1]

Sebastian Reymundo

September 21, 2025

Multi-Part Part Studios
