alexandrasalazarz-lgtm/FunBioG14./ENTREGABLES/Entregable 5/Ivanna Rodriguez/Detailed_Drawings.pdf

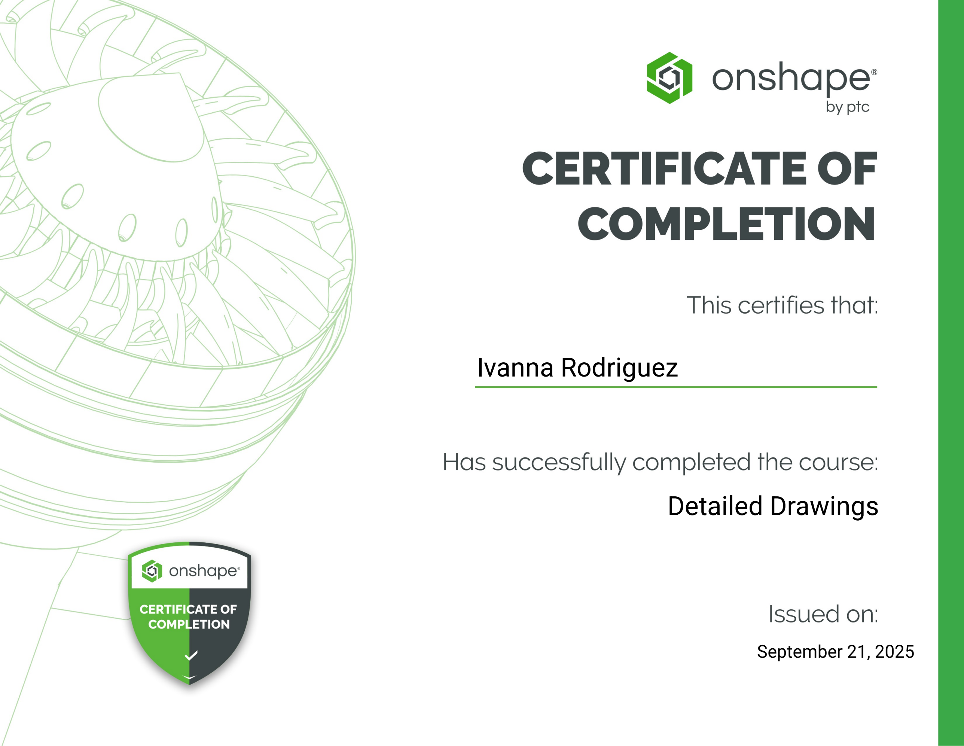
[picture p144: page 1]

Ivanna Rodriguez

September 21, 2025

Detailed Drawings
