alexandrasalazarz-lgtm/FunBioG14./ENTREGABLES/Entregable 5/Ivanna Rodriguez/Introductio_to_part_Studios.pdf

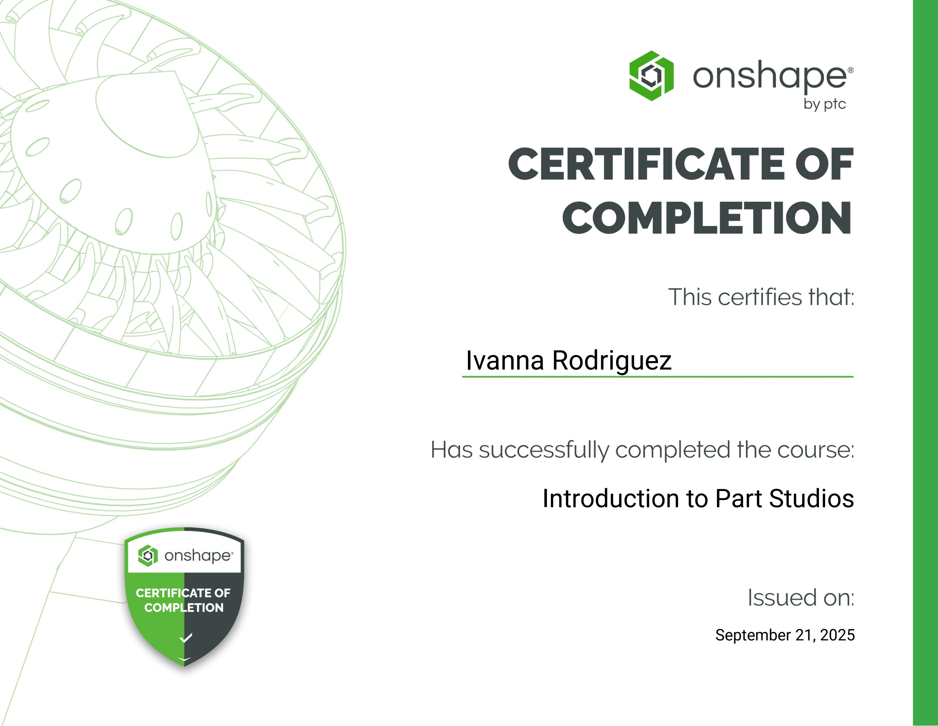
[picture p145: page 1]

Ivanna Rodriguez

Introduction to Part Studios

September 21, 2025
