alexandrasalazarz-lgtm/FunBioG14./ENTREGABLES/Entregable 5/Ivanna Rodriguez/Introduction_to_Sketching.pdf

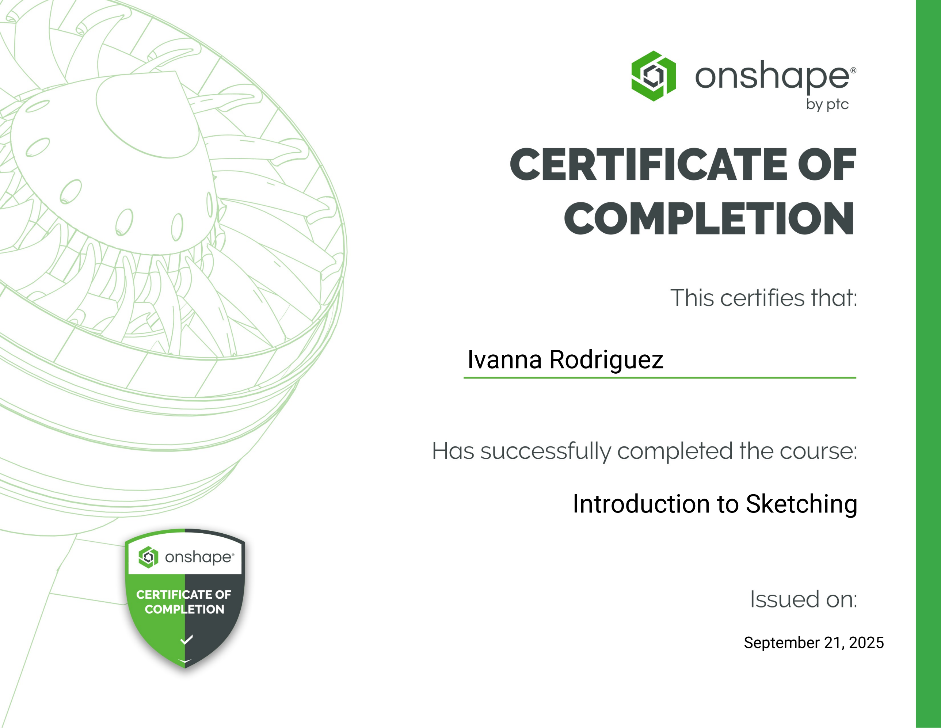
[picture p146: page 1]

Ivanna Rodriguez

Introduction to Sketching

September 21, 2025
