alexandrasalazarz-lgtm/FunBioG14./ENTREGABLES/Entregable 5/Ivanna Rodriguez/Multi-Part_Studios.pdf

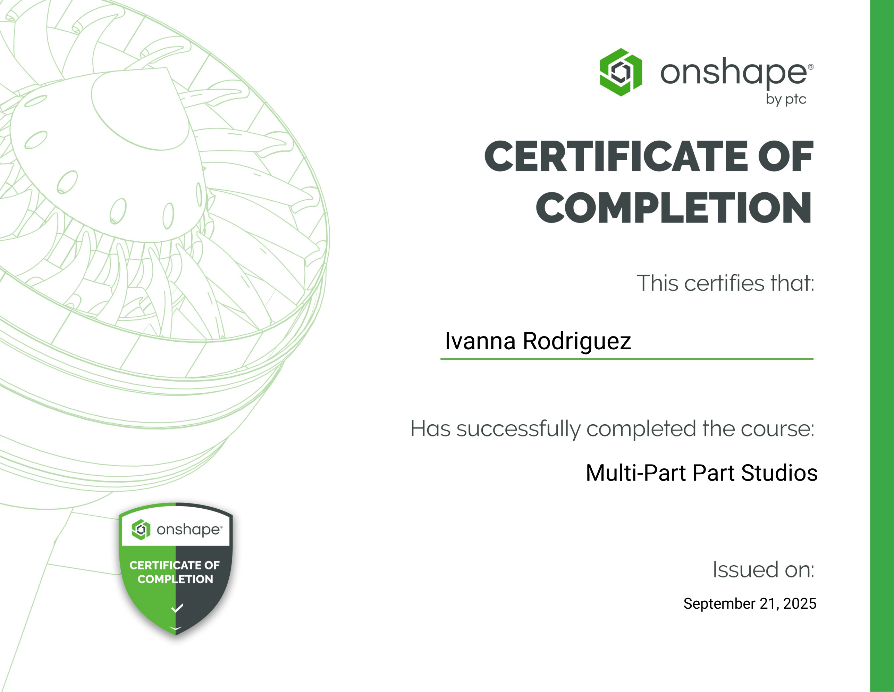
[picture p147: page 1]

Ivanna Rodriguez

September 21, 2025

Multi-Part Part Studios
