alexandrasalazarz-lgtm/FunBioG14./ENTREGABLES/Entregable 5/Ivanna Rodriguez/Onshape_Fundamentals.pdf

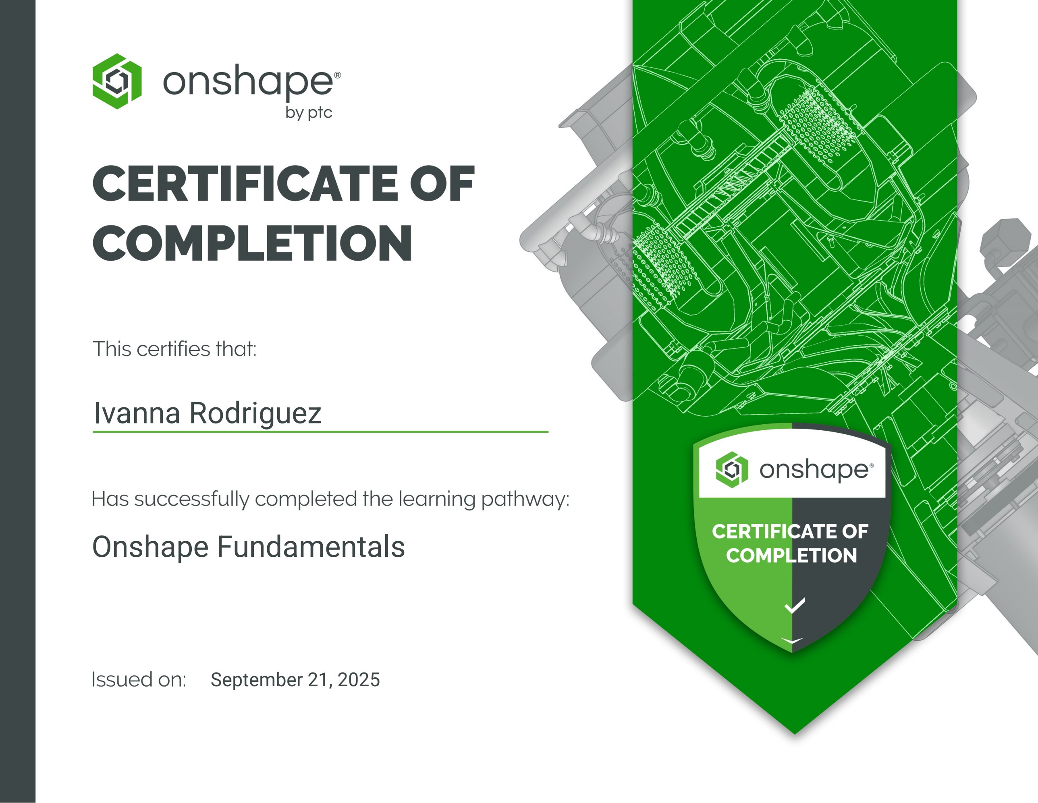
[picture p148: page 1]

Onshape Fundamentals

September 21, 2025

Ivanna Rodriguez
