alexandrasalazarz-lgtm/FunBioG14./ENTREGABLES/Entregable 5/Luciana Saenz/luciana-saenz-2a0414bc-6588-4cc1-b5d2-1da495238edb-certificate.pdf

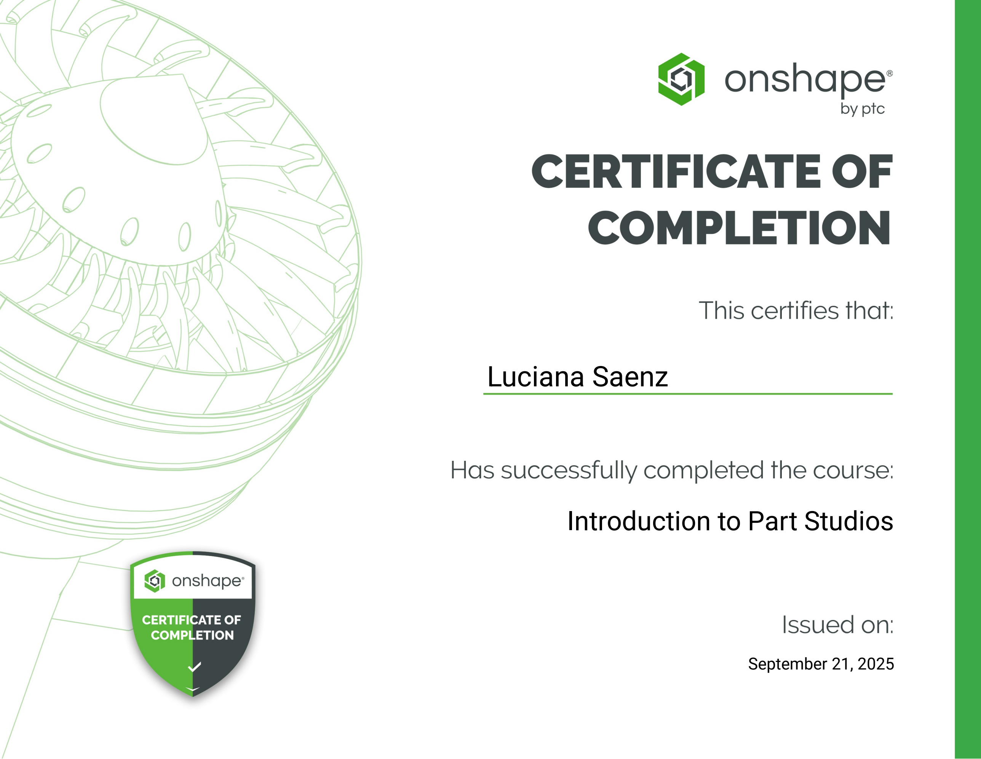
[picture p149: page 1]

Luciana Saenz

Introduction to Part Studios

September 21, 2025
