alexandrasalazarz-lgtm/FunBioG14./ENTREGABLES/Entregable 5/Luciana Saenz/luciana-saenz-43757262-1f7c-4425-9df9-dd577cf9f2c8-certificate.pdf

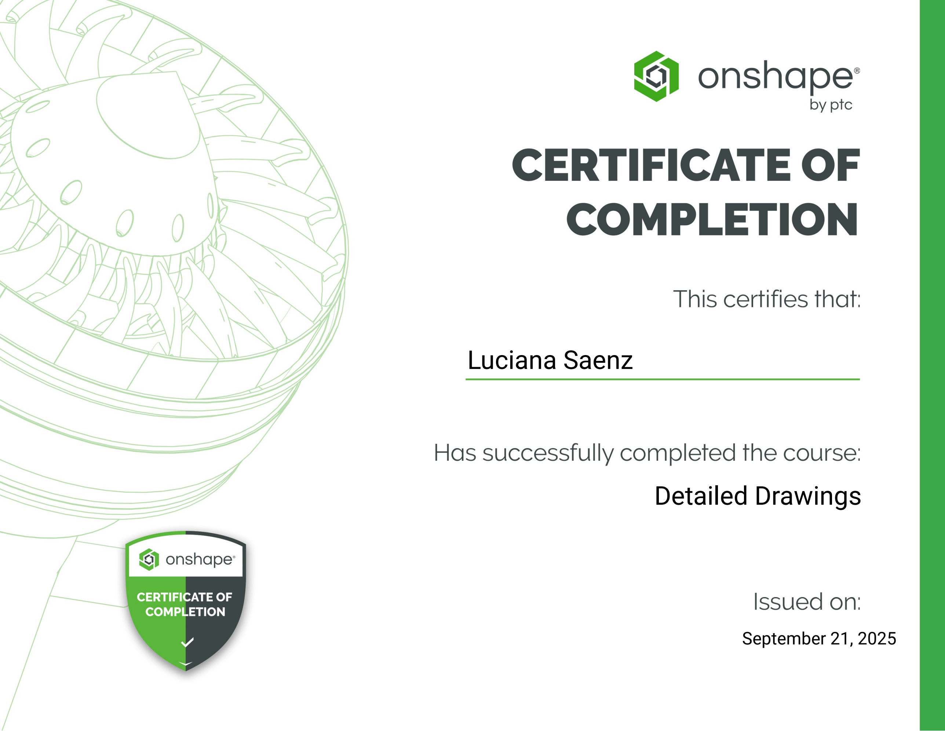
[picture p150: page 1]

Luciana Saenz

September 21, 2025

Detailed Drawings
