alexandrasalazarz-lgtm/FunBioG14./ENTREGABLES/Entregable 5/Luciana Saenz/luciana-saenz-a3716f97-c1ba-4916-89c7-1004da7511c2-certificate.pdf

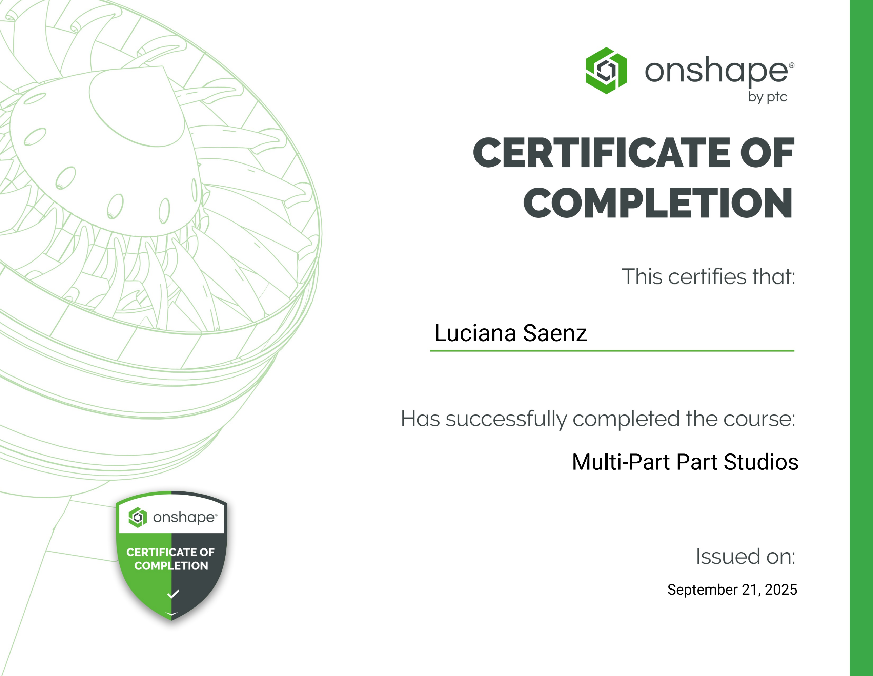
[picture p151: page 1]

Luciana Saenz

September 21, 2025

Multi-Part Part Studios
