alexandrasalazarz-lgtm/FunBioG14./ENTREGABLES/Entregable 5/Luciana Saenz/luciana-saenz-c7eff77e-fc75-4fa5-a055-071f5c8927fd-certificate.pdf

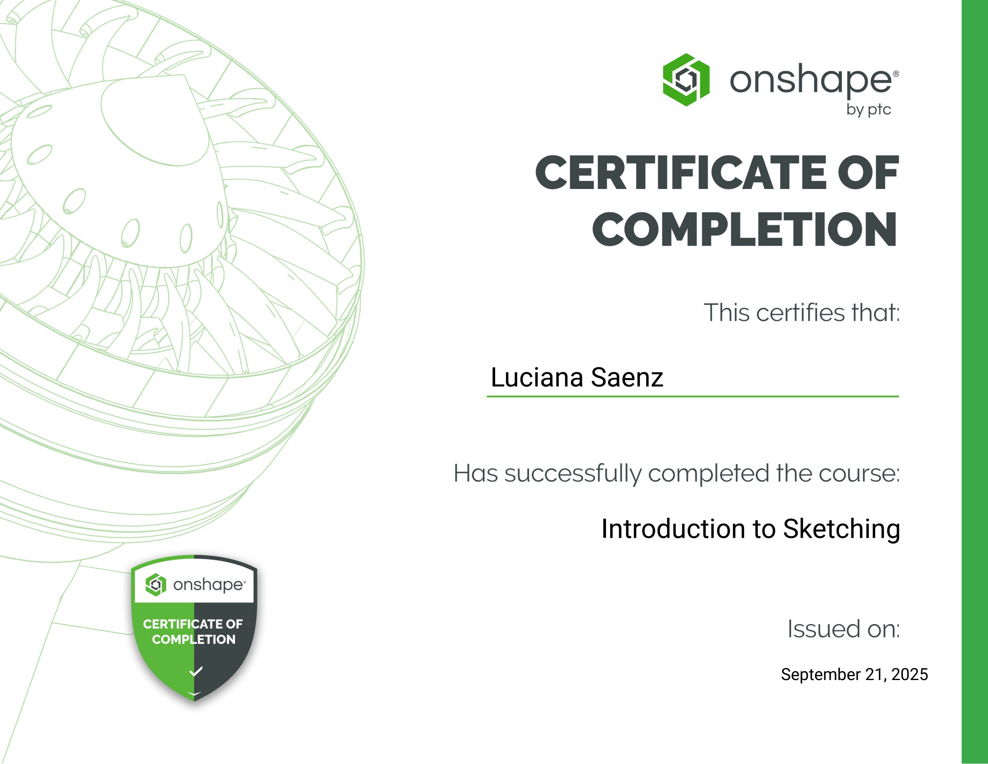
[picture p152: page 1]

Luciana Saenz

Introduction to Sketching

September 21, 2025
