alexandrasalazarz-lgtm/FunBioG14./ENTREGABLES/Entregable 5/Jared Neciosup/jared-neciosup-Detailed drawings.pdf

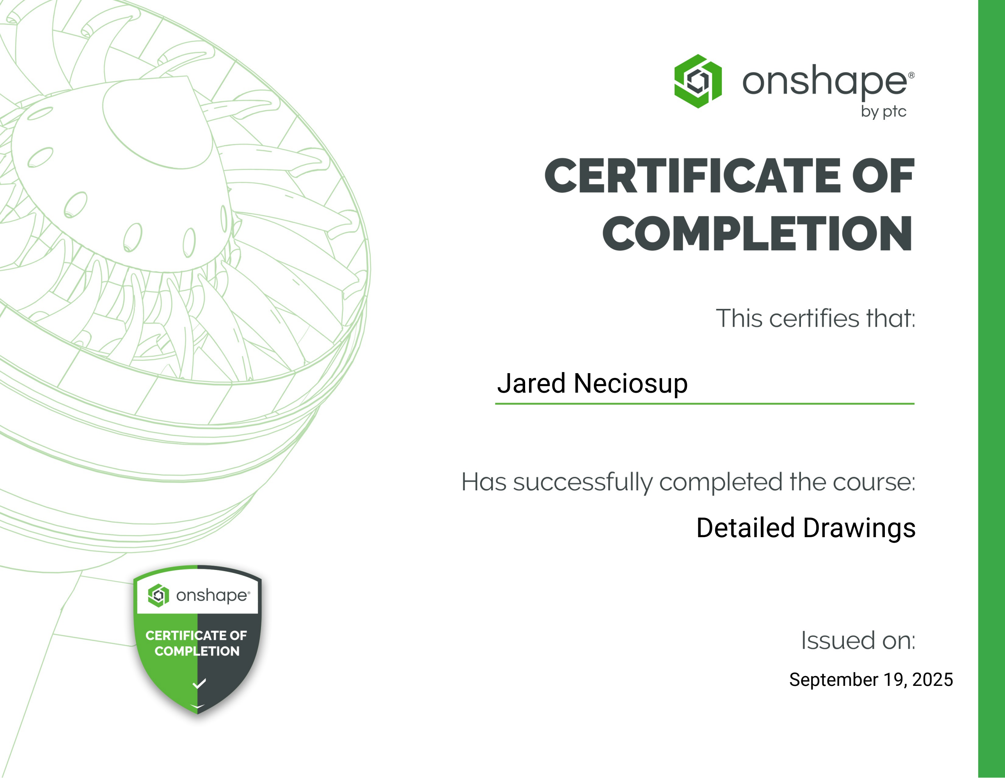
[picture p153: page 1]

Jared Neciosup

September 19, 2025

Detailed Drawings
