alexandrasalazarz-lgtm/FunBioG14./ENTREGABLES/Entregable 5/Jared Neciosup/jared-neciosup-Introducing to part studios.pdf

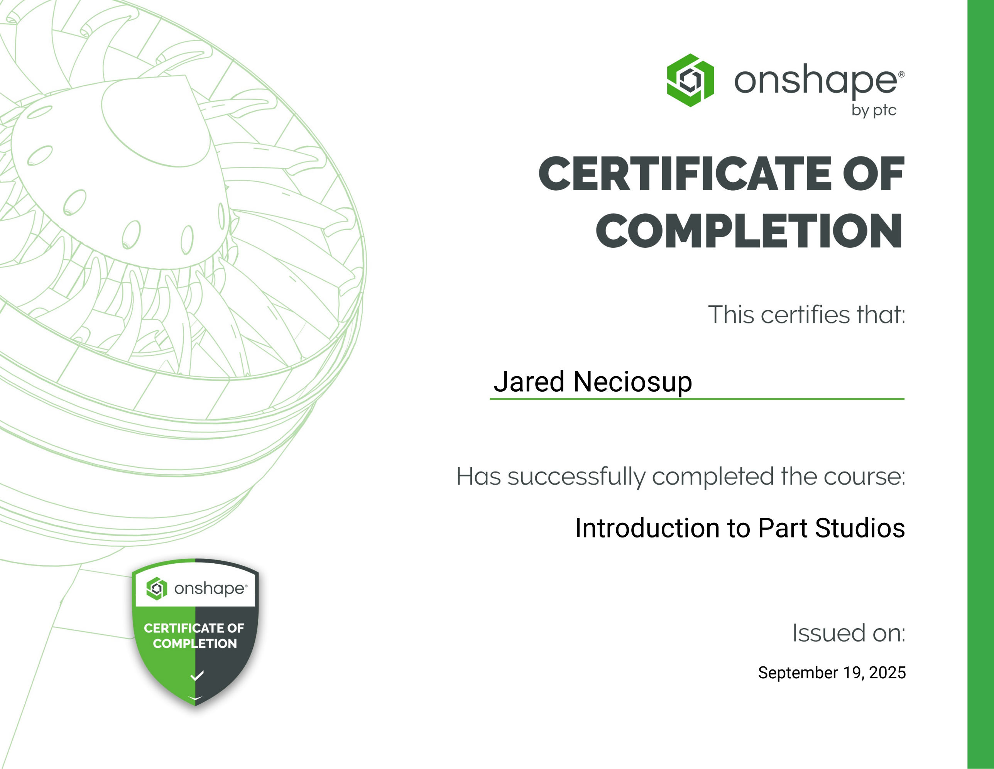
[picture p154: page 1]

Jared Neciosup

Introduction to Part Studios

September 19, 2025
