alexandrasalazarz-lgtm/FunBioG14./ENTREGABLES/Entregable 5/Jared Neciosup/jared-neciosup-Introducing to sketching.pdf

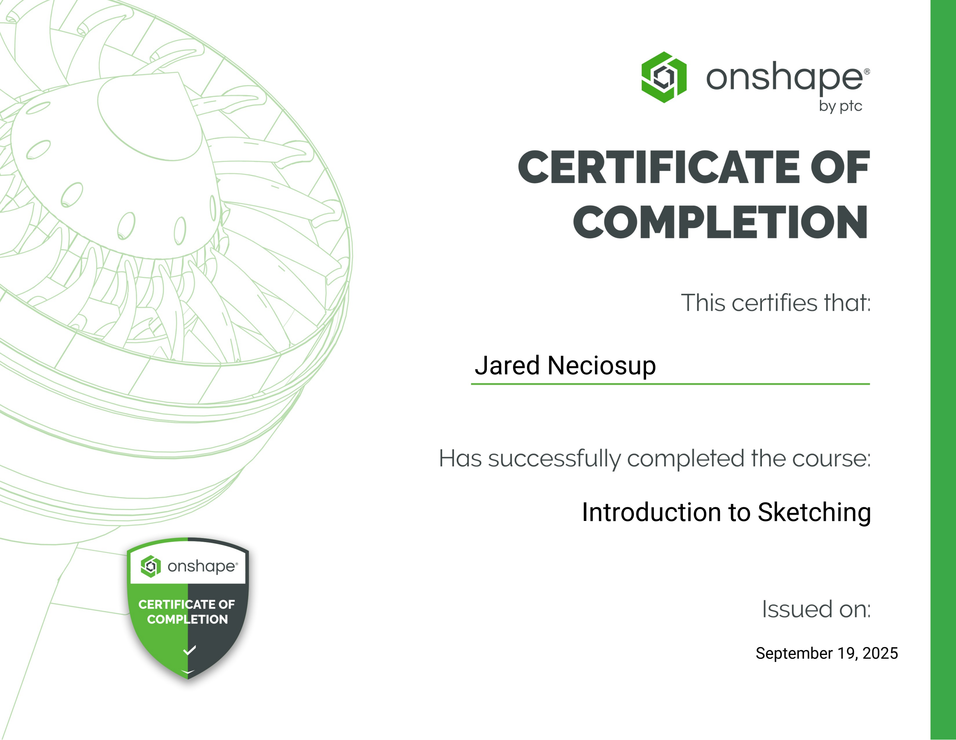
[picture p155: page 1]

Jared Neciosup

Introduction to Sketching

September 19, 2025
