alexandrasalazarz-lgtm/FunBioG14./ENTREGABLES/Entregable 5/Jared Neciosup/jared-neciosup-Multi-part part studios.pdf

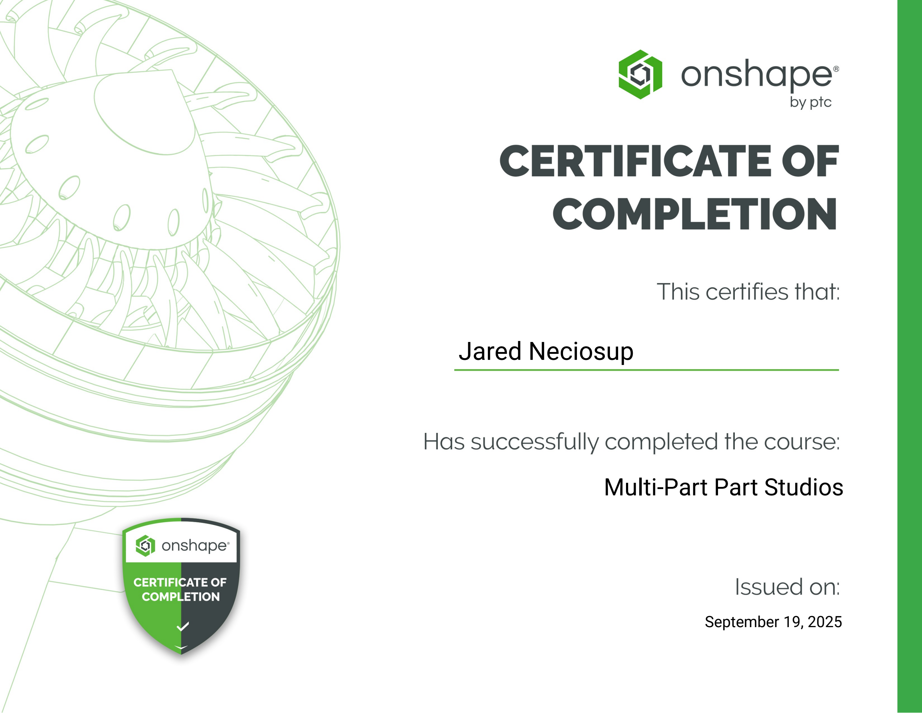
[picture p156: page 1]

Jared Neciosup

September 19, 2025

Multi-Part Part Studios
