alexandrasalazarz-lgtm/FunBioG14./ENTREGABLES/Entregable 5/Tatiana Quispe/tati-quispe-cueva-5732071c-76d9-4768-a462-c8400071c49d-certificate.pdf

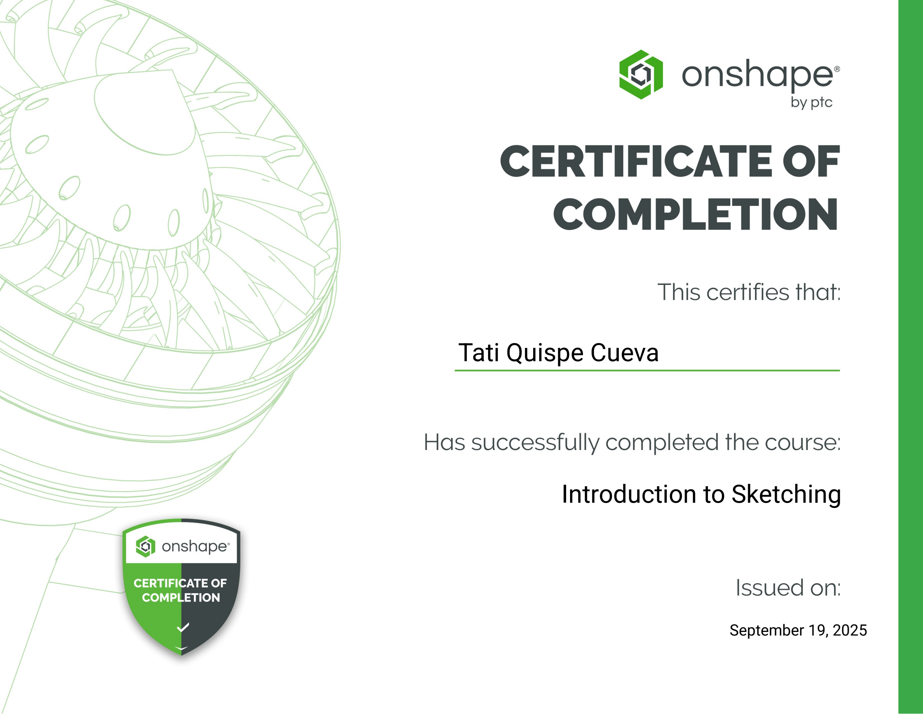
[picture p157: page 1]

Tati Quispe Cueva

Introduction to Sketching

September 19, 2025
