alexandrasalazarz-lgtm/FunBioG14./ENTREGABLES/Entregable 5/Tatiana Quispe/tati-quispe-cueva-716db872-f709-43a3-add0-48aa18133794-certificate.pdf

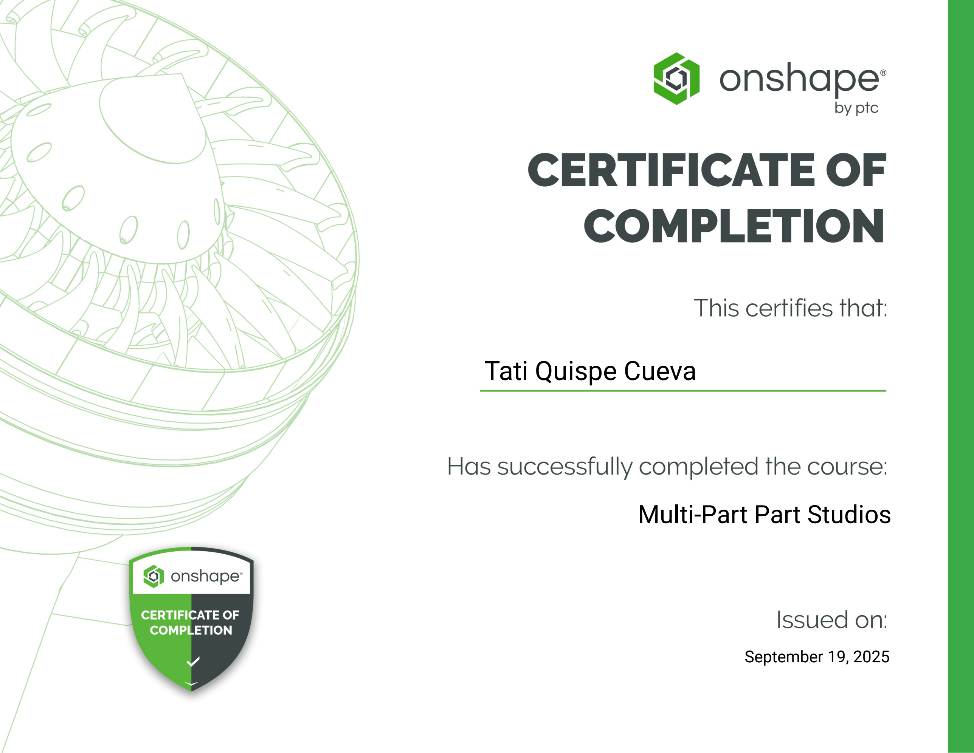
[picture p158: page 1]

Tati Quispe Cueva

September 19, 2025

Multi-Part Part Studios
