alexandrasalazarz-lgtm/FunBioG14./ENTREGABLES/Entregable 5/Tatiana Quispe/tati-quispe-cueva-b019b6f6-2f97-4a5a-9bf3-3dede9ec85be-certificate.pdf

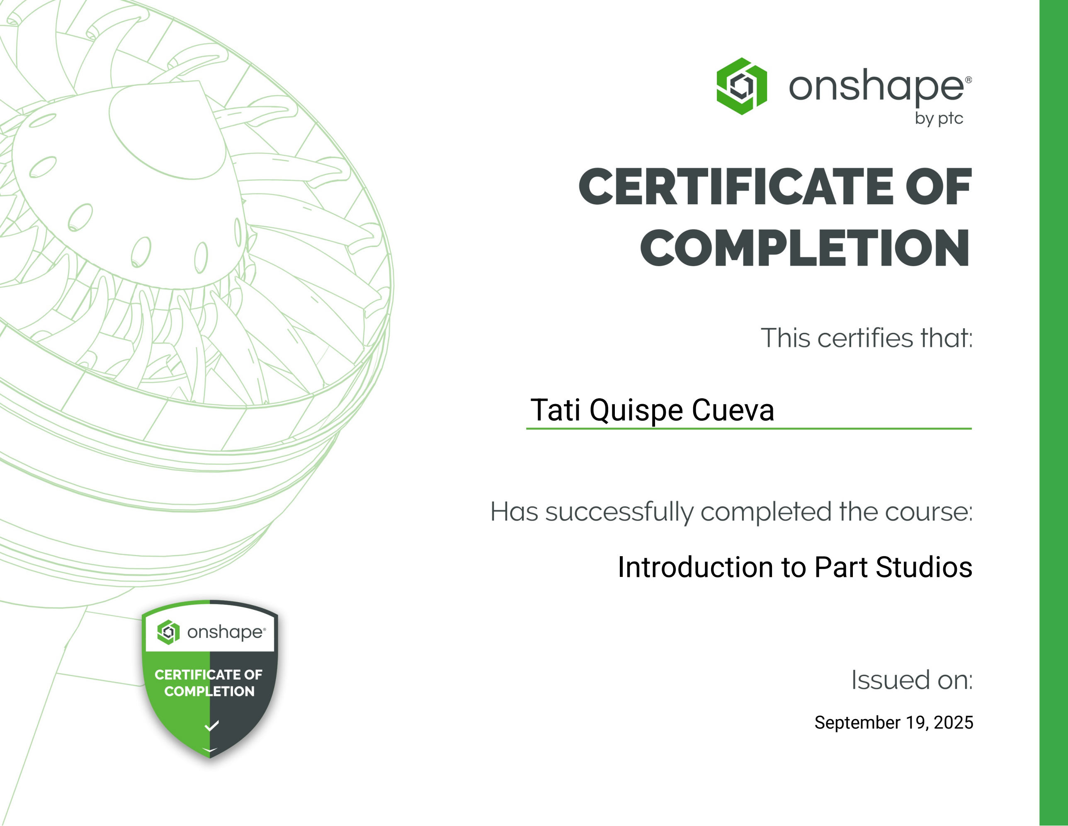
[picture p159: page 1]

Tati Quispe Cueva

Introduction to Part Studios

September 19, 2025
