alexandrasalazarz-lgtm/FunBioG14./ENTREGABLES/Entregable 5/Tatiana Quispe/tati-quispe-cueva-ff24f048-0d31-4d2f-88b8-625def9fc5f3-certificate.pdf

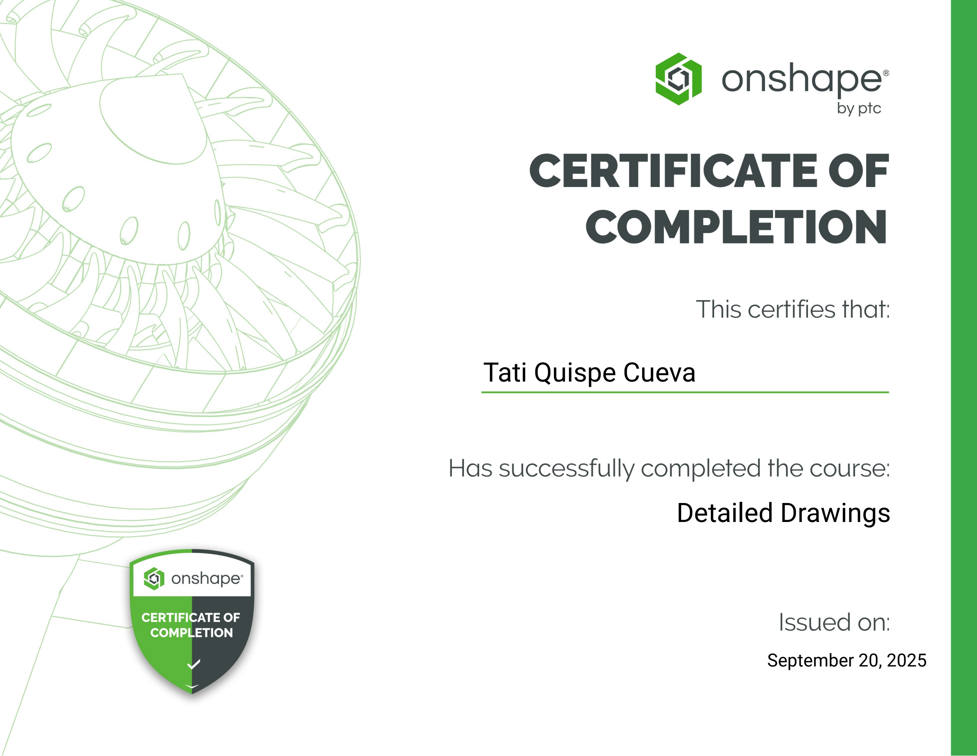
[picture p160: page 1]

Tati Quispe Cueva

September 20, 2025

Detailed Drawings
