alexandrasalazarz-lgtm/FunBioG14./ENTREGABLES/Entregable 5/Alexandra Salazar/alexandra-salazar-6406fd9c-1378-43a9-8818-74959abc0f3b-certificate.pdf

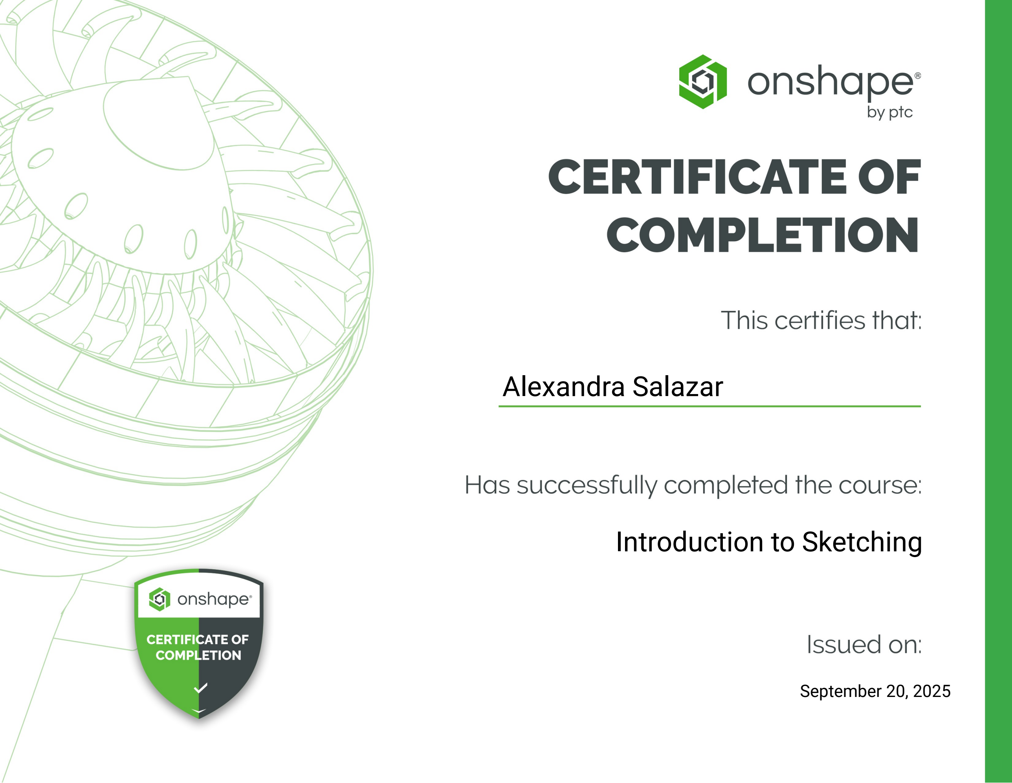
[picture p161: page 1]

Alexandra Salazar

Introduction to Sketching

September 20, 2025
