alexandrasalazarz-lgtm/FunBioG14./ENTREGABLES/Entregable 5/Alexandra Salazar/alexandra-salazar-64ac8e81-e8d6-45aa-80d1-1613ca4f6050-certificate.pdf

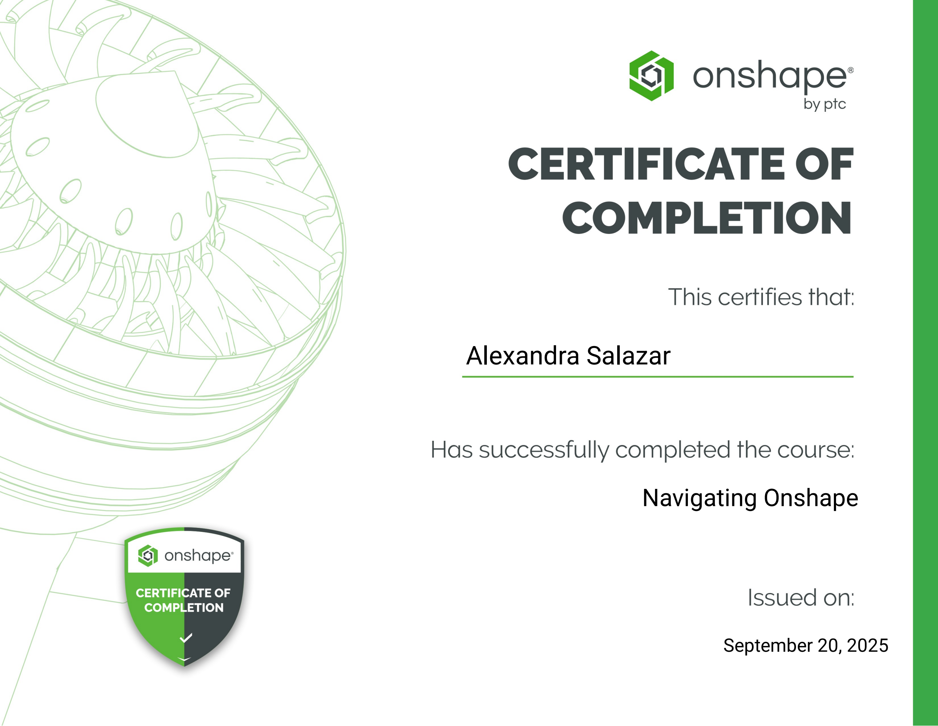
[picture p162: page 1]

Alexandra Salazar

Navigating Onshape

September 20, 2025
