alexandrasalazarz-lgtm/FunBioG14./ENTREGABLES/Entregable 5/Alexandra Salazar/alexandra-salazar-85727d8a-2f7b-46ec-8166-655db6c9df9a-certificate.pdf

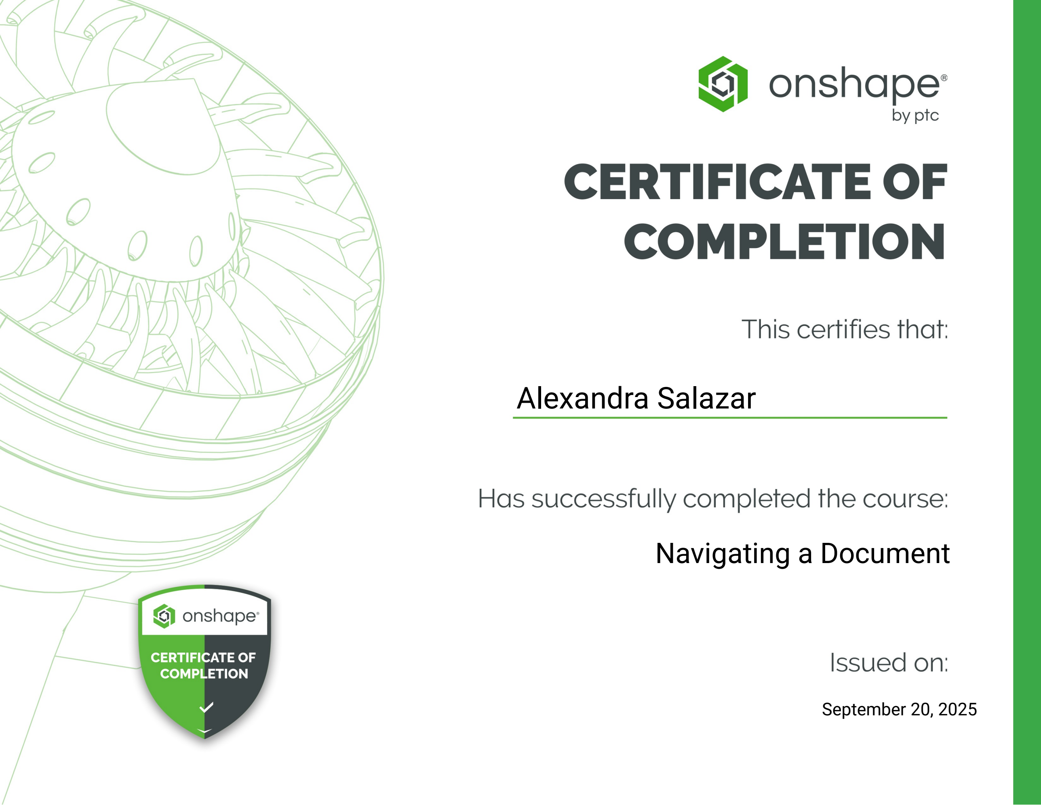
[picture p163: page 1]

Alexandra Salazar

September 20, 2025

Navigating a Document
