alexandrasalazarz-lgtm/FunBioG14./ENTREGABLES/Entregable 5/Alexandra Salazar/alexandra-salazar-f7a0821a-a05a-4848-9388-87ca7ebe514d-certificate.pdf

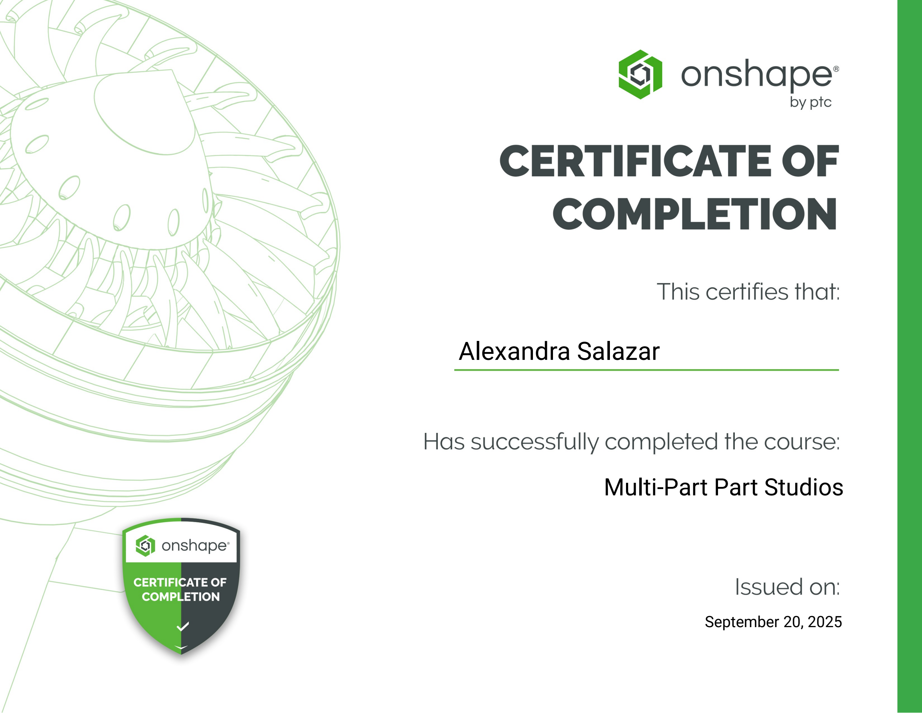
[picture p164: page 1]

Alexandra Salazar

September 20, 2025

Multi-Part Part Studios
